grodansparadis/vscp-din-wireless-esp32-can-z102/design-documents/Z102_img/Z102_50.jpg

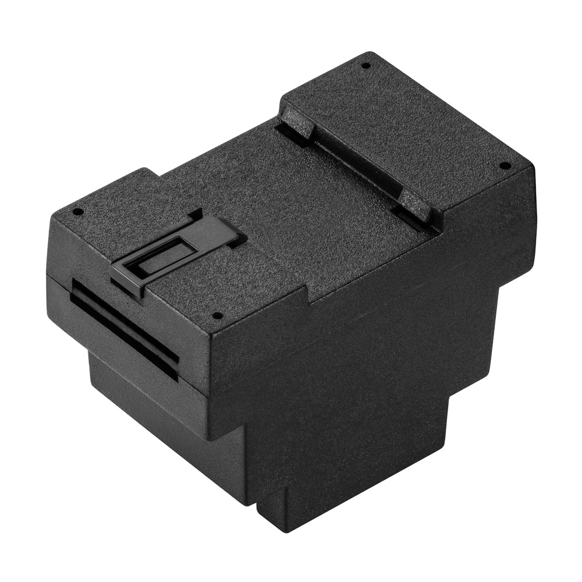
design-documents/Z102_img/Z102_50.jpg
