grodansparadis/vscp-din-wireless-esp32-can-z102/images/addr2line_error.png

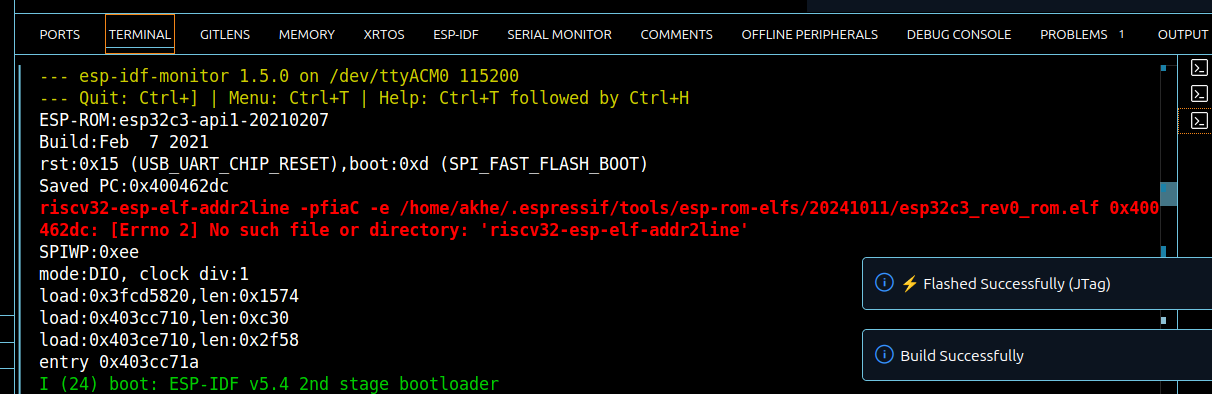
images/addr2line_error.png
