grodansparadis/vscp-din-wireless-esp32-can-z102/firmware/main/websrv.c

/*
  Web Server

  This file is part of the VSCP (https://www.vscp.org)

  The MIT License (MIT)
  Copyright (C) 2022-2026 Ake Hedman, the VSCP project <info@vscp.org>

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
  THE SOFTWARE IS PROVIDED "AS IS", WITHOUT WARRANTY OF ANY KIND, EXPRESS OR
  IMPLIED, INCLUDING BUT NOT LIMITED TO THE WARRANTIES OF MERCHANTABILITY,
  FITNESS FOR A PARTICULAR PURPOSE AND NONINFRINGEMENT. IN NO EVENT SHALL THE
  AUTHORS OR COPYRIGHT HOLDERS BE LIABLE FOR ANY CLAIM, DAMAGES OR OTHER
  LIABILITY, WHETHER IN AN ACTION OF CONTRACT, TORT OR OTHERWISE, ARISING FROM,
  OUT OF OR IN CONNECTION WITH THE SOFTWARE OR THE USE OR OTHER DEALINGS IN THE
  SOFTWARE.
*/

#include <stdio.h>
#include <string.h>
#include <ctype.h>
#include <stdarg.h>
#include <sys/param.h>
#include <sys/unistd.h>
#include <sys/stat.h>
#include <sys/socket.h>
#include <netinet/in.h>
#include <arpa/inet.h>
#include <dirent.h>

#include <esp_system.h>
#include <esp_chip_info.h>
#include <esp_flash_spi_init.h>
#include <esp_flash.h>
#include <esp_wifi.h>
#include <esp_mac.h>
#include <esp_ota_ops.h>
#include <esp_timer.h>
#include <esp_err.h>
#include <esp_log.h>
#include <nvs_flash.h>
#include <esp_http_server.h>

#include <esp_event_base.h>
#include <esp_tls_crypto.h>
#include <esp_vfs.h>
#include <esp_spiffs.h>
#include <network_provisioning/manager.h>
#include <cJSON.h>

#include <freertos/FreeRTOS.h>
#include <freertos/semphr.h>

#include <vscp.h>
#include <vscp-class.h>
#include <vscp-type.h>
#include <vscp-firmware-helper.h>

#include "urldecode.h"

#include "mqtt.h"
#include "main.h"
#include "vscp-ws1.h"
#include "websocksrv.h"
#include "websrv.h"
#include "udpsrv.h"
#include "build/build_counter.h"

#if !CONFIG_HTTPD_WS_SUPPORT
#error This code cannot be used unless HTTPD_WS_SUPPORT is enabled in esp-http-server component configuration
#endif

#ifdef CONFIG_EXAMPLE_PROV_TRANSPORT_BLE
#include <network_provisioning/scheme_ble.h>
#endif /* PROV_EXAMPLE_TRANSPORT_BLE */

#ifdef CONFIG_EXAMPLE_PROV_TRANSPORT_SOFTAP
#include <network_provisioning/scheme_softap.h>
#endif /* PROV_EXAMPLE_TRANSPORT_SOFTAP */

// #define MIN(a, b) (((a) < (b)) ? (a) : (b))
// #define MAX(a, b) (((a) > (b)) ? (a) : (b))

// From app_main
void
startOTA(void);
int
app_initiate_firmware_upload(const char *url);

// External from main
extern nvs_handle_t g_nvsHandle;
extern node_persistent_config_t g_persistent;
extern vprintf_like_t g_stdLogFunc;
extern transport_t tr_websockets;
extern transport_t tr_canapi;
extern transport_t tr_monitor;

// Extern from webnsocksrv
extern httpd_handle_t g_websocket_srv;

#define TAG __func__

static const char *
web_ui_version(const esp_app_desc_t *appDescr)
{
  static char s_ui_ver[64];
  const char *base = "0.0.0";

  if ((NULL != appDescr) && ('\0' != appDescr->version[0])) {
    base = appDescr->version;
  }

  snprintf(s_ui_ver, sizeof(s_ui_ver), "%s+b%d", base, BUILD_COUNTER);
  return s_ui_ver;
}

// Keep a short in-memory rolling log for the web UI.
#define WEB_LOG_RING_SIZE 200
#define WEB_LOG_LINE_MAX  192

typedef struct {
  uint32_t seq;
  char line[WEB_LOG_LINE_MAX];
} web_log_item_t;

static web_log_item_t g_web_log_ring[WEB_LOG_RING_SIZE];
static uint32_t g_web_log_seq = 0;
vprintf_like_t g_stdLogFunc   = NULL;
static SemaphoreHandle_t g_web_log_mutex = NULL;
static volatile bool s_web_log_route_in_progress = false;

static int web_log_vprintf(const char *fmt, va_list args);
static void web_log_capture_line(const char *line);
static esp_err_t logs_get_handler(httpd_req_t *req);
static esp_err_t logstream_get_handler(httpd_req_t *req);
static void web_log_hook_init(void);

// Max length a file path can have on storage
#define FILE_PATH_MAX (ESP_VFS_PATH_MAX + CONFIG_SPIFFS_OBJ_NAME_LEN)

// Chunk buffer size
#define CHUNK_BUFSIZE 8192

#define IS_FILE_EXT(filename, ext) (strcasecmp(&filename[strlen(filename) - sizeof(ext) + 1], ext) == 0)

// Prototypes

///////////////////////////////////////////////////////////////////////////////
// web_log_capture_line
//

static void
web_log_capture_line(const char *line)
{
  if ((NULL == line) || ('\0' == *line) || (NULL == g_web_log_mutex)) {
    return;
  }

  if (pdTRUE != xSemaphoreTake(g_web_log_mutex, pdMS_TO_TICKS(5))) {
    return;
  }

  uint32_t seq = ++g_web_log_seq;
  size_t idx   = (size_t) ((seq - 1U) % WEB_LOG_RING_SIZE);
  g_web_log_ring[idx].seq = seq;

  size_t j = 0;
  for (size_t i = 0; (line[i] != '\0') && (j < (WEB_LOG_LINE_MAX - 1)); ++i) {
    char c = line[i];
    if (('\r' == c) || ('\n' == c)) {
      if ((j > 0) && (' ' != g_web_log_ring[idx].line[j - 1])) {
        g_web_log_ring[idx].line[j++] = ' ';
      }
      continue;
    }
    g_web_log_ring[idx].line[j++] = c;
  }
  g_web_log_ring[idx].line[j] = '\0';

  xSemaphoreGive(g_web_log_mutex);
}

///////////////////////////////////////////////////////////////////////////////
// web_log_route_message
//
// Route log message to configured destination based on logType setting
//

static void
web_log_route_message(const char *message)
{
  if (NULL == message || '\0' == message[0]) {
    return;
  }

  // Route based on configured log type
  switch (g_persistent.logType) {
    
    case LOG_TYPE_UDP:
      // Send log message via configured logging destination.
      udpsrv_broadcast_message((const uint8_t *) message,
                               strlen(message),
                               g_persistent.logUrl,
                               g_persistent.logPort);
      break;

    case LOG_TYPE_MQTT:
      // Send log message via MQTT (if enabled)
      if (g_persistent.enableMqtt && strlen(g_persistent.logMqttTopic)) {
        mqtt_log((char *) message);
      }
      break;

    case LOG_TYPE_STD:
    case LOG_TYPE_TCP:
    case LOG_TYPE_HTTP:
    case LOG_TYPE_VSCP:
    case LOG_TYPE_NONE:
    default:
      // These are handled by the default logging mechanism or not used for syslog
      break;
  }
}

///////////////////////////////////////////////////////////////////////////////
// web_log_vprintf
//

static int
web_log_vprintf(const char *fmt, va_list args)
{
  if (NULL != fmt) {
    char line[WEB_LOG_LINE_MAX] = { 0 };
    va_list copy;
    va_copy(copy, args);
    int n = vsnprintf(line, sizeof(line), fmt, copy);
    va_end(copy);

    if (n > 0) {
      web_log_capture_line(line);

      // Prevent recursive routing when transport code itself logs.
      if (!s_web_log_route_in_progress) {
        s_web_log_route_in_progress = true;
        web_log_route_message(line);
        s_web_log_route_in_progress = false;
      }
    }
  }

  if (NULL != g_stdLogFunc) {
    return g_stdLogFunc(fmt, args);
  }

  return vprintf(fmt, args);
}

///////////////////////////////////////////////////////////////////////////////
// web_log_hook_init
//

static void
web_log_hook_init(void)
{
  if (NULL == g_web_log_mutex) {
    g_web_log_mutex = xSemaphoreCreateMutex();
  }

  if ((NULL != g_web_log_mutex) && (NULL == g_stdLogFunc)) {
    g_stdLogFunc = esp_log_set_vprintf(web_log_vprintf);
    ESP_LOGI(TAG, "Web log capture enabled");
  }
}

///////////////////////////////////////////////////////////////////////////////
// backup_add_hex_field
//

static void
backup_add_hex_field(cJSON *obj, const char *name, const uint8_t *data, size_t len)
{
  if ((NULL == obj) || (NULL == name) || (NULL == data) || (0 == len)) {
    return;
  }

  char *hex = (char *) calloc((len * 2) + 1, 1);
  if (NULL == hex) {
    return;
  }

  for (size_t i = 0; i < len; i++) {
    sprintf(hex + (i * 2), "%02X", data[i]);
  }

  cJSON_AddStringToObject(obj, name, hex);
  free(hex);
}

static uint32_t
backup_secret_seed(const char *field_name)
{
  uint32_t seed     = 2166136261u;
  const char *fixed = "VSCP-CFG-BACKUP-V1";

  for (size_t i = 0; fixed[i] != '\0'; i++) {
    seed ^= (uint8_t) fixed[i];
    seed *= 16777619u;
  }

  if (NULL != field_name) {
    for (size_t i = 0; field_name[i] != '\0'; i++) {
      seed ^= (uint8_t) field_name[i];
      seed *= 16777619u;
    }
  }

  if (0 == seed) {
    seed = 0x1A2B3C4Du;
  }

  return seed;
}

static uint32_t
backup_secret_next(uint32_t *state)
{
  *state ^= (*state << 13);
  *state ^= (*state >> 17);
  *state ^= (*state << 5);
  return *state;
}

static bool
backup_encrypt_to_hex(const char *field_name, const uint8_t *in, size_t in_len, char *out, size_t out_len)
{
  if ((NULL == in) || (NULL == out)) {
    return false;
  }

  if (out_len < ((in_len * 2) + 5)) {
    return false;
  }

  memcpy(out, "enc:", 4);
  uint32_t st = backup_secret_seed(field_name);

  for (size_t i = 0; i < in_len; i++) {
    uint8_t b = in[i] ^ (uint8_t) (backup_secret_next(&st) & 0xFF);
    sprintf(out + 4 + (i * 2), "%02X", b);
  }

  out[4 + (in_len * 2)] = '\0';
  return true;
}

static bool
backup_decrypt_from_hex(const char *field_name, const char *in, uint8_t *out, size_t out_len, size_t *written)
{
  if ((NULL == field_name) || (NULL == in) || (NULL == out)) {
    return false;
  }

  if (0 != strncmp(in, "enc:", 4)) {
    return false;
  }

  const char *hex = in + 4;
  size_t hex_len  = strlen(hex);
  if ((0 == hex_len) || (0 != (hex_len % 2))) {
    return false;
  }

  size_t need = hex_len / 2;
  if (need > out_len) {
    return false;
  }

  uint32_t st = backup_secret_seed(field_name);
  for (size_t i = 0; i < need; i++) {
    char h1 = hex[i * 2];
    char h2 = hex[(i * 2) + 1];
    if (!isxdigit((unsigned char) h1) || !isxdigit((unsigned char) h2)) {
      return false;
    }

    uint8_t hi = (uint8_t) ((h1 <= '9') ? (h1 - '0') : (10 + (tolower((unsigned char) h1) - 'a')));
    uint8_t lo = (uint8_t) ((h2 <= '9') ? (h2 - '0') : (10 + (tolower((unsigned char) h2) - 'a')));
    uint8_t b  = (uint8_t) ((hi << 4) | lo);
    out[i]     = b ^ (uint8_t) (backup_secret_next(&st) & 0xFF);
  }

  if (NULL != written) {
    *written = need;
  }

  return true;
}

static void
backup_add_encrypted_str_field(cJSON *obj, const char *name, const char *plain)
{
  if ((NULL == obj) || (NULL == name) || (NULL == plain)) {
    return;
  }

  size_t plain_len = strlen(plain);
  if (0 == plain_len) {
    cJSON_AddStringToObject(obj, name, "");
    return;
  }

  size_t out_len = (plain_len * 2) + 5;
  char *enc      = (char *) calloc(out_len, 1);
  if (NULL == enc) {
    cJSON_AddStringToObject(obj, name, "");
    return;
  }

  if (backup_encrypt_to_hex(name, (const uint8_t *) plain, plain_len, enc, out_len)) {
    cJSON_AddStringToObject(obj, name, enc);
  }
  else {
    cJSON_AddStringToObject(obj, name, "");
  }

  free(enc);
}

static void
backup_add_encrypted_blob_field(cJSON *obj, const char *name, const uint8_t *data, size_t data_len)
{
  if ((NULL == obj) || (NULL == name) || (NULL == data)) {
    return;
  }

  size_t out_len = (data_len * 2) + 5;
  char *enc      = (char *) calloc(out_len, 1);
  if (NULL == enc) {
    return;
  }

  if (backup_encrypt_to_hex(name, data, data_len, enc, out_len)) {
    cJSON_AddStringToObject(obj, name, enc);
  }

  free(enc);
}

//-----------------------------------------------------------------------------
//                               Start Basic Auth
//-----------------------------------------------------------------------------

///////////////////////////////////////////////////////////////////////////////
// http_auth_basic
//

static char *
http_auth_basic(const char *username, const char *password)
{
  int out;
  char *user_info = NULL;
  char *digest    = NULL;
  size_t n        = 0;
  asprintf(&user_info, "%s:%s", username, password);
  if (!user_info) {
    ESP_LOGE(TAG, "No enough memory for user information");
    return NULL;
  }
  esp_crypto_base64_encode(NULL, 0, &n, (const unsigned char *) user_info, strlen(user_info));

  /* 6: The length of the "Basic " string
   * n: Number of bytes for a base64 encode format
   * 1: Number of bytes for a reserved which be used to fill zero
   */
  digest = calloc(6 + n + 1, 1);
  if (digest) {
    strcpy(digest, "Basic ");
    esp_crypto_base64_encode((unsigned char *) digest + 6,
                             n,
                             (size_t *) &out,
                             (const unsigned char *) user_info,
                             strlen(user_info));
  }
  free(user_info);
  return digest;
}

///////////////////////////////////////////////////////////////////////////////
// info_get_handler
//
// HTTP GET handler for info page
//

static esp_err_t
info_get_handler(httpd_req_t *req)
{
  // esp_err_t rv;
  char *buf;
  char *temp;

  buf = (char *) calloc(CHUNK_BUFSIZE, 1);
  if (NULL == buf) {
    return ESP_ERR_NO_MEM;
  }

  temp = (char *) calloc(80, 1);
  if (NULL == temp) {
    return ESP_ERR_NO_MEM;
  }

  esp_chip_info_t chip_info;
  esp_chip_info(&chip_info);

  const esp_app_desc_t *appDescr = esp_app_get_description();

  sprintf(buf, WEBPAGE_START_TEMPLATE, g_persistent.nodeName, "Technical Node Info");
  httpd_resp_send_chunk(req, buf, HTTPD_RESP_USE_STRLEN);

  sprintf(buf, "<table style='width:100%%;margin-left: auto; margin-right: auto;'>");
  httpd_resp_send_chunk(req, buf, HTTPD_RESP_USE_STRLEN);

  // * * * system * * *);
  sprintf(buf, "<tr><td class='infoheader'>System</td><td></td></tr>");
  httpd_resp_send_chunk(req, buf, HTTPD_RESP_USE_STRLEN);

  sprintf(buf, "<tr style='padding: 25px;'><td class=\"name\">Chip type:</td>");
  httpd_resp_send_chunk(req, buf, HTTPD_RESP_USE_STRLEN);
  switch (chip_info.model) {

    case CHIP_ESP32:
      // printf("ESP32\n");
      sprintf(buf, "<td class=\"prop\">ESP32</td></tr>");
      break;

    case CHIP_ESP32S2:
      // printf("ESP32-S2\n");
      sprintf(buf, "<td class=\"prop\">ESP32-S2</td></tr>");
      break;

    case CHIP_ESP32S3:
      // printf("ESP32-S3\n");
      sprintf(buf, "<td class=\"prop\">ESP32-S3</td></tr>");
      break;

    case CHIP_ESP32C3:
      // printf("ESP32-C3\n");
      sprintf(buf, "<td class=\"prop\">ESP32-C3</td></tr>");
      break;

    case CHIP_ESP32H2:
      // printf("ESP32-H2\n");
      sprintf(buf, "<td class=\"prop\">ESP32-H2</td></tr>");
      break;

    case CHIP_ESP32C2:
      // printf("ESP32-C2\n");
      sprintf(buf, "<td class=\"prop\">ESP32-C2</td></tr>");
      break;

    default:
      // printf("Unknown\n");
      sprintf(buf, "<td class=\"prop\">Unknown</td></tr>");
      break;
  }
  httpd_resp_send_chunk(req, buf, HTTPD_RESP_USE_STRLEN);

  sprintf(buf, "<tr><td class=\"name\">Number of cores:</td><td class=\"prop\">%d</td></tr>", chip_info.cores);
  httpd_resp_send_chunk(req, buf, HTTPD_RESP_USE_STRLEN);

  // printf("Number of cores: %d \n", chip_info.cores);

  // Chip comm features
  sprintf(temp,
          "%s%s%s%s",
          (chip_info.features & CHIP_FEATURE_WIFI_BGN) ? "WiFi " : "",
          (chip_info.features & CHIP_FEATURE_BT) ? "BT " : "",
          (chip_info.features & CHIP_FEATURE_BLE) ? "BLE " : "",
          (chip_info.features & CHIP_FEATURE_IEEE802154) ? "802.15.4 " : "");
  sprintf(buf, "<tr><td class=\"name\">Chip comm features:</td><td class=\"prop\">%s</td></tr>", temp);
  httpd_resp_send_chunk(req, buf, HTTPD_RESP_USE_STRLEN);

  wifi_country_t country;
  esp_wifi_get_country(&country);
  // printf("Wifi country code: %c%c%c\n", country.cc[0],country.cc[1],country.cc[2]);
  sprintf(buf,
          "<tr><td class=\"name\">Wifi country code:</td><td class=\"prop\">%c%c%c</td></tr>",
          country.cc[0],
          country.cc[1],
          country.cc[2]);
  httpd_resp_send_chunk(req, buf, HTTPD_RESP_USE_STRLEN);

  sprintf(temp, "%s", (chip_info.features & CHIP_FEATURE_EMB_FLASH) ? "Yes" : "No");
  sprintf(buf, "<tr><td class=\"name\">Embedded flash:</td><td class=\"prop\">%s</td></tr>", temp);
  httpd_resp_send_chunk(req, buf, HTTPD_RESP_USE_STRLEN);

  sprintf(temp, "%s", (chip_info.features & CHIP_FEATURE_EMB_PSRAM) ? "Yes" : "No");
  sprintf(buf, "<tr><td class=\"name\">Embedded psram:</td><td class=\"prop\">%s</td></tr>", temp);
  httpd_resp_send_chunk(req, buf, HTTPD_RESP_USE_STRLEN);

  // sprintf(temp, "%d", chip_info.revision);
  sprintf(buf, "<tr><td class=\"name\">Silicon revision:</td><td class=\"prop\">%d</td></tr>", chip_info.revision);
  httpd_resp_send_chunk(req, buf, HTTPD_RESP_USE_STRLEN);

  uint32_t chipId;
  esp_flash_read_id(NULL, &chipId);
  // printf("Flash chip id: %04lX\n", chipId);
  sprintf(buf, "<tr><td class=\"name\">Flash chip id:</td><td class=\"prop\">%04lX</td></tr>", chipId);
  httpd_resp_send_chunk(req, buf, HTTPD_RESP_USE_STRLEN);

  uint64_t uniqueId;
  esp_flash_read_unique_chip_id(NULL, &uniqueId);
  // printf("Unique flash chip id: %08llX\n", uniqueId);
  sprintf(buf, "<tr><td class=\"name\">Unique flash chip id:</td><td class=\"prop\">%08llX</td></tr>", uniqueId);
  httpd_resp_send_chunk(req, buf, HTTPD_RESP_USE_STRLEN);

  uint32_t sizeFlash;
  esp_flash_get_size(NULL, &sizeFlash);
  sprintf(temp, "%s", (chip_info.features & CHIP_FEATURE_EMB_FLASH) ? "(embedded)" : "(external)");
  // printf("%luMB %s flash\n",
  //        sizeFlash / (1024 * 1024),
  //        (chip_info.features & CHIP_FEATURE_EMB_FLASH) ? "embedded" : "external");
  sprintf(buf,
          "<tr><td class=\"name\">Flash size:</td><td class=\"prop\">%s %lu MB</td></tr>",
          temp,
          sizeFlash / (1024 * 1024));
  httpd_resp_send_chunk(req, buf, HTTPD_RESP_USE_STRLEN);

  // get chip id
  // chipId = String((uint32_t) ESP.getEfuseMac(), HEX);
  // chipId.toUpperCase();
  // printf("Chip id: %s\n", chipId.c_str());

  // printf("esp-idf version: %s\n", esp_get_idf_version());
  sprintf(buf, "<tr><td class=\"name\">esp-idf version:</td><td class=\"prop\">%s</td></tr>", esp_get_idf_version());
  httpd_resp_send_chunk(req, buf, HTTPD_RESP_USE_STRLEN);

  // printf("Free heap size: %lu\n", esp_get_free_heap_size());
  sprintf(buf,
          "<tr><td class=\"name\">Free heap size:</td><td class=\"prop\">%lu kB (%lu)</td></tr>",
          esp_get_free_heap_size() / 1024,
          esp_get_free_heap_size());
  httpd_resp_send_chunk(req, buf, HTTPD_RESP_USE_STRLEN);

  // printf("Min free heap size: %lu\n", esp_get_minimum_free_heap_size());
  sprintf(buf,
          "<tr><td class=\"name\">Min free heap size:</td><td class=\"prop\">%lu kB (%lu)</td></tr>",
          esp_get_minimum_free_heap_size() / 1024,
          esp_get_minimum_free_heap_size());
  httpd_resp_send_chunk(req, buf, HTTPD_RESP_USE_STRLEN);

  // printf("Last reset reson: ");
  switch (esp_reset_reason()) {
    case ESP_RST_POWERON:
      sprintf(temp, "Reset due to power-on event.\n");
      break;
    case ESP_RST_EXT:
      sprintf(temp, "Reset by external pin (not applicable for ESP32.\n");
      break;
    case ESP_RST_SW:
      sprintf(temp, "Software reset via esp_restart.\n");
      break;
    case ESP_RST_PANIC:
      sprintf(temp, "Software reset due to exception/panic.\n");
      break;
    case ESP_RST_INT_WDT:
      sprintf(temp, "Reset (software or hardware) due to interrupt watchdog.\n");
      break;
    case ESP_RST_TASK_WDT:
      sprintf(temp, "Reset due to task watchdog.\n");
      break;
    case ESP_RST_WDT:
      sprintf(temp, "Reset due to other watchdogs.\n");
      break;
    case ESP_RST_DEEPSLEEP:
      sprintf(temp, "Reset after exiting deep sleep mode.\n");
      break;
    case ESP_RST_BROWNOUT:
      sprintf(temp, "Brownout reset (software or hardware.\n");
      break;
    case ESP_RST_SDIO:
      sprintf(temp, "Reset over SDIO.\n");
      break;
    case ESP_RST_UNKNOWN:
    default:
      sprintf(temp, "Reset reason can not be determined.\n");
      break;
  }
  sprintf(buf, "<tr><td class=\"name\">Last reset reason:</td><td class=\"prop\">%s</td></tr>", temp);
  httpd_resp_send_chunk(req, buf, HTTPD_RESP_USE_STRLEN);

  sprintf(buf, "<tr><td class=\"name\">Number of reboots:</td><td class=\"prop\">%lu</td></tr>", g_persistent.bootCnt);
  httpd_resp_send_chunk(req, buf, HTTPD_RESP_USE_STRLEN);

  char *bufguid = (char *) calloc(50, 1);
  if (NULL != bufguid) {
    vscp_fwhlp_writeGuidToString(bufguid, g_persistent.guid);
    sprintf(buf, "<tr><td class=\"name\">GUID:</td><td class=\"prop\">%s</td></tr>", bufguid);
    httpd_resp_send_chunk(req, buf, HTTPD_RESP_USE_STRLEN);
    free(bufguid);
  }

  // -------------------------------------------------------------------------

  // * * *  Application * * *
  // sprintf(buf, "<tr><td>Application</td><td></td></tr>");
  sprintf(buf, "<tr><td class='infoheader'>Application</td><td></td></tr>");
  httpd_resp_send_chunk(req, buf, HTTPD_RESP_USE_STRLEN);

  int64_t time = esp_timer_get_time();
  int64_t seconds = time / 1000000;
  sprintf(buf,
          "<tr><td class=\"name\">Uptime:</td><td class=\"prop\">%lldT%02lld:%02lld:%02lld</td></tr>",
          seconds / (3600 * 24),
          (seconds % (3600 * 24)) / 3600,
          (seconds % 3600) / 60,
          seconds % 60);
  httpd_resp_send_chunk(req, buf, HTTPD_RESP_USE_STRLEN);

  if (NULL != appDescr) {
    // sprintf(temp,"%s",appDescr->project_name);
    sprintf(buf, "<tr><td class=\"name\">Application:</td><td class=\"prop\">%s</td></tr>", appDescr->project_name);
    httpd_resp_send_chunk(req, buf, HTTPD_RESP_USE_STRLEN);

    // sprintf(temp,"Application ver: %s\n",appDescr->version);
        sprintf(buf,
          "<tr><td class=\"name\">Application ver:</td><td class=\"prop\">%s</td></tr>",
          web_ui_version(appDescr));
    httpd_resp_send_chunk(req, buf, HTTPD_RESP_USE_STRLEN);

    // sprintf(temp,"Application ver: %s %s\n",appDescr->date,appDescr->time);
    sprintf(buf,
            "<tr><td class=\"name\">Compile time:</td><td class=\"prop\">%s %s</td></tr>",
            appDescr->date,
            appDescr->time);
    httpd_resp_send_chunk(req, buf, HTTPD_RESP_USE_STRLEN);

    // sprintf(temp,"idf ver: %s\n",appDescr->idf_ver);
    sprintf(buf, "<tr><td class=\"name\">Compiled w/ idf ver:</td><td class=\"prop\">%s</td></tr>", appDescr->idf_ver);
    httpd_resp_send_chunk(req, buf, HTTPD_RESP_USE_STRLEN);
  }

  // * * *  CAN/TWAI * * *
  sprintf(buf, "<tr><td class='infoheader'>CAN/TWAI Interface</td><td></td></tr>");
  httpd_resp_send_chunk(req, buf, HTTPD_RESP_USE_STRLEN);

  // CAN Mode
  const char *canModeStr = (g_persistent.canMode == 0) ? "Normal" : "Listen Only";
  sprintf(buf, "<tr><td class=\"name\">CAN Mode:</td><td class=\"prop\">%s</td></tr>", canModeStr);
  httpd_resp_send_chunk(req, buf, HTTPD_RESP_USE_STRLEN);

  // CAN Speed
  const char *canSpeedStr;
  switch (g_persistent.canSpeed) {
    case 0:
      canSpeedStr = "5 Kbps";
      break;
    case 1:
      canSpeedStr = "10 Kbps";
      break;
    case 2:
      canSpeedStr = "20 Kbps";
      break;
    case 3:
      canSpeedStr = "25 Kbps";
      break;
    case 4:
      canSpeedStr = "50 Kbps";
      break;
    case 5:
      canSpeedStr = "100 Kbps";
      break;
    case 6:
      canSpeedStr = "125 Kbps";
      break;
    case 7:
      canSpeedStr = "250 Kbps";
      break;
    case 8:
      canSpeedStr = "500 Kbps";
      break;
    case 9:
      canSpeedStr = "800 Kbps";
      break;
    case 10:
      canSpeedStr = "1000 Kbps";
      break;
    default:
      canSpeedStr = "Unknown";
      break;
  }
  sprintf(buf, "<tr><td class=\"name\">CAN Speed:</td><td class=\"prop\">%s</td></tr>", canSpeedStr);
  httpd_resp_send_chunk(req, buf, HTTPD_RESP_USE_STRLEN);

  // CAN Filter
  sprintf(buf,
          "<tr><td class=\"name\">CAN Filter:</td><td class=\"prop\">0x%08X</td></tr>",
          (unsigned int) g_persistent.canFilter);
  httpd_resp_send_chunk(req, buf, HTTPD_RESP_USE_STRLEN);

  // Messages Sent
  sprintf(buf,
          "<tr><td class=\"name\">Messages Sent:</td><td class=\"prop\">%u</td></tr>",
          (unsigned int) g_persistent.nSent);
  httpd_resp_send_chunk(req, buf, HTTPD_RESP_USE_STRLEN);

  // Messages Received
  sprintf(buf,
          "<tr><td class=\"name\">Messages Received:</td><td class=\"prop\">%u</td></tr>",
          (unsigned int) g_persistent.nRecv);
  httpd_resp_send_chunk(req, buf, HTTPD_RESP_USE_STRLEN);

  // Total Errors
  sprintf(buf,
          "<tr><td class=\"name\">Total Errors:</td><td class=\"prop\">%u</td></tr>",
          (unsigned int) g_persistent.nErr);
  httpd_resp_send_chunk(req, buf, HTTPD_RESP_USE_STRLEN);

  // Last Error Code
  sprintf(buf,
          "<tr><td class=\"name\">Last Error Code:</td><td class=\"prop\">0x%08X</td></tr>",
          (unsigned int) g_persistent.lastError);
  httpd_resp_send_chunk(req, buf, HTTPD_RESP_USE_STRLEN);

  // * * *  Connection * * *
  sprintf(buf, "<tr><td class='infoheader'>Connection</td><td></td></tr>");
  httpd_resp_send_chunk(req, buf, HTTPD_RESP_USE_STRLEN);

  wifi_mode_t mode;
  esp_wifi_get_mode(&mode);
  switch (mode) {

    case WIFI_MODE_STA:
      sprintf(temp, "STA\n");
      break;

    case WIFI_MODE_AP:
      sprintf(temp, "AP\n");
      break;

    case WIFI_MODE_APSTA:
      sprintf(temp, "APSTA\n");
      break;

    case WIFI_MODE_NULL:
    default:
      sprintf(temp, "unknown\n");
      break;
  };
  // sprintf(temp,"Wifi mode: ");
  sprintf(buf, "<tr><td class=\"name\">Wifi mode:</td><td class=\"prop\">%s</td></tr>", temp);
  httpd_resp_send_chunk(req, buf, HTTPD_RESP_USE_STRLEN);

  wifi_sta_list_t sta;
  esp_wifi_ap_get_sta_list(&sta);
  // printf("Stations: %d\n",sta.num);
  sprintf(buf, "<tr><td class=\"name\">Stations:</td><td class=\"prop\">%d</td></tr>", sta.num);
  httpd_resp_send_chunk(req, buf, HTTPD_RESP_USE_STRLEN);

  wifi_ap_record_t ap_info;
  esp_wifi_sta_get_ap_info(&ap_info);
  // printf("bssid: " MACSTR "\n", MAC2STR(ap_info.bssid));
  sprintf(buf, "<tr><td class=\"name\">bssid:</td><td class=\"prop\">" MACSTR "</td></tr>", MAC2STR(ap_info.bssid));
  httpd_resp_send_chunk(req, buf, HTTPD_RESP_USE_STRLEN);

  // printf("ssid: %s\n", ap_info.ssid);
  sprintf(buf, "<tr><td class=\"name\">ssid:</td><td class=\"prop\">%s</td></tr>", ap_info.ssid);
  httpd_resp_send_chunk(req, buf, HTTPD_RESP_USE_STRLEN);

  // printf("channel: %d (%d)\n", ap_info.primary, ap_info.second);
  sprintf(buf,
          "<tr><td class=\"name\">channel:</td><td class=\"prop\">%d (%d)</td></tr>",
          ap_info.primary,
          ap_info.second);
  httpd_resp_send_chunk(req, buf, HTTPD_RESP_USE_STRLEN);

  // printf("signal strength: %d\n", ap_info.rssi);
  if (ap_info.rssi > -30) {
    sprintf(temp, "Perfect");
  }
  else if (ap_info.rssi > -50) {
    sprintf(temp, "Excellent");
  }
  else if (ap_info.rssi > -60) {
    sprintf(temp, "Good");
  }
  else if (ap_info.rssi > -67) {
    sprintf(temp, "Limited");
  }
  else if (ap_info.rssi > -70) {
    sprintf(temp, "Poor");
  }
  else if (ap_info.rssi > -80) {
    sprintf(temp, "Unstable");
  }
  else {
    sprintf(temp, "Unusable");
  }

  sprintf(buf,
          "<tr><td class=\"name\">signal strength:</td><td class=\"prop\">%d dBm ( %d%% = %s)</td></tr>",
          ap_info.rssi,
          (2 * (ap_info.rssi + 100)),
          temp);
  httpd_resp_send_chunk(req, buf, HTTPD_RESP_USE_STRLEN);

  // printf("Mode: 11%s%s%s %s %s",
  //           ap_info.phy_11b ? "b" : "",
  //           ap_info.phy_11g ? "g" : "",
  //           ap_info.phy_11n ? "n" : "",
  //           ap_info.phy_lr ? "lr" : "",
  //           ap_info.wps ? "wps" : "");
  // printf("\nAuth mode of AP: ");
  switch (ap_info.authmode) {

    case WIFI_AUTH_OPEN:
      sprintf(temp, "open\n");
      break;

    case WIFI_AUTH_WEP:
      sprintf(temp, "wep\n");
      break;

    case WIFI_AUTH_WPA_PSK:
      sprintf(temp, "wpa-psk\n");
      break;

    case WIFI_AUTH_WPA2_PSK:
      sprintf(temp, "wpa2-psk\n");
      break;

    case WIFI_AUTH_WPA_WPA2_PSK:
      sprintf(temp, "wpa-wpa2-psk\n");
      break;

    case WIFI_AUTH_WPA2_ENTERPRISE:
      sprintf(temp, "wpa2-enterprise\n");
      break;

    case WIFI_AUTH_WPA3_PSK:
      sprintf(temp, "wpa3-psk\n");
      break;

    case WIFI_AUTH_WPA2_WPA3_PSK:
      sprintf(temp, "wpa2-wpa3-psk\n");
      break;

    case WIFI_AUTH_WAPI_PSK:
      sprintf(temp, "wpa2-wapi-psk\n");
      break;

    case WIFI_AUTH_OWE:
      sprintf(temp, "wpa2-wapi-psk\n");
      break;

    default:
      sprintf(temp, "unknown\n");
      break;
  }

  sprintf(buf, "<tr><td class=\"name\">Auth mode of AP:</td><td class=\"prop\">%s</td></tr>", temp);
  httpd_resp_send_chunk(req, buf, HTTPD_RESP_USE_STRLEN);

  uint8_t mac[6];
  esp_wifi_get_mac(ESP_MAC_WIFI_STA, mac);
  // printf("Wifi STA MAC address: " MACSTR "\n", MAC2STR(mac));
  sprintf(buf,
          "<tr><td class=\"name\">Wifi STA MAC address:</td><td class=\"prop\">" MACSTR "</td></tr>",
          MAC2STR(mac));
  httpd_resp_send_chunk(req, buf, HTTPD_RESP_USE_STRLEN);

  esp_wifi_get_mac(ESP_MAC_WIFI_SOFTAP, mac);
  // printf("Wifi SOFTAP MAC address: " MACSTR "\n", MAC2STR(mac));
  sprintf(buf,
          "<tr><td class=\"name\">Wifi SOFTAP MAC address:</td><td class=\"prop\">" MACSTR "</td></tr>",
          MAC2STR(mac));
  httpd_resp_send_chunk(req, buf, HTTPD_RESP_USE_STRLEN);

  esp_netif_t *netif = NULL;
  netif              = esp_netif_get_handle_from_ifkey("WIFI_STA_DEF");
  esp_netif_ip_info_t ifinfo;
  if (NULL != netif) {
    esp_netif_get_ip_info(netif, &ifinfo);
    // printf("IP address (wifi): " IPSTR "\n", IP2STR(&ifinfo.ip));
    sprintf(buf,
            "<tr><td class=\"name\">IP address (wifi):</td><td class=\"prop\">" IPSTR "</td></tr>",
            IP2STR(&ifinfo.ip));
    httpd_resp_send_chunk(req, buf, HTTPD_RESP_USE_STRLEN);

    // printf("Subnet Mask: " IPSTR "\n", IP2STR(&ifinfo.netmask));
    sprintf(buf,
            "<tr><td class=\"name\">Subnet Mask:</td><td class=\"prop\">" IPSTR "</td></tr>",
            IP2STR(&ifinfo.netmask));
    httpd_resp_send_chunk(req, buf, HTTPD_RESP_USE_STRLEN);

    // printf("Gateway: " IPSTR "\n", IP2STR(&ifinfo.gw));
    sprintf(buf, "<tr><td class=\"name\">Gateway:</td><td class=\"prop\">" IPSTR "</td></tr>", IP2STR(&ifinfo.gw));
    httpd_resp_send_chunk(req, buf, HTTPD_RESP_USE_STRLEN);

    esp_netif_dns_info_t dns;
    esp_netif_get_dns_info(netif, ESP_NETIF_DNS_MAIN, &dns);
    // printf("DNS DNS Server1: " IPSTR "\n", IP2STR(&dns.ip.u_addr.ip4));
    sprintf(buf,
            "<tr><td class=\"name\">DNS Server1:</td><td class=\"prop\">" IPSTR "</td></tr>",
            IP2STR(&dns.ip.u_addr.ip4));
    httpd_resp_send_chunk(req, buf, HTTPD_RESP_USE_STRLEN);
    esp_netif_get_dns_info(netif, ESP_NETIF_DNS_BACKUP, &dns);

    // printf("DNS Server2: " IPSTR "\n", IP2STR(&dns.ip.u_addr.ip4));
    sprintf(buf,
            "<tr><td class=\"name\">DNS Server2:</td><td class=\"prop\">" IPSTR "</td></tr>",
            IP2STR(&dns.ip.u_addr.ip4));
    httpd_resp_send_chunk(req, buf, HTTPD_RESP_USE_STRLEN);
  }

  sprintf(buf, "</table>");
  httpd_resp_send_chunk(req, buf, HTTPD_RESP_USE_STRLEN);

  sprintf(buf, WEBPAGE_END_TEMPLATE, web_ui_version(appDescr), g_persistent.nodeName);
  httpd_resp_send_chunk(req, buf, HTTPD_RESP_USE_STRLEN);

  httpd_resp_send_chunk(req, NULL, 0);

  free(buf);
  free(temp);

  return ESP_OK;
}

// URI handler for getting uploaded files
httpd_uri_t info = { .uri = "/info", .method = HTTP_GET, .handler = info_get_handler, .user_ctx = NULL };

///////////////////////////////////////////////////////////////////////////////
// reset_get_handler
//
// HTTP GET handler for reset of machine
//

static esp_err_t
reset_get_handler(httpd_req_t *req)
{
  const char *resp_str = "<html><head><meta charset='utf-8'><meta http-equiv=\"refresh\" content=\"2;url=index.html\" "
                         "/></head><body><h1>The system is restarting...</h1></body></html>";
  httpd_resp_send(req, resp_str, HTTPD_RESP_USE_STRLEN);

  // Let content render
  vTaskDelay(2000 / portTICK_PERIOD_MS);

  // esp_wifi_disconnect();
  // vTaskDelay(2000 / portTICK_PERIOD_MS);
  esp_restart();
  return ESP_OK;
}

httpd_uri_t reset = { .uri = "/reset", .method = HTTP_GET, .handler = reset_get_handler, .user_ctx = NULL };

///////////////////////////////////////////////////////////////////////////////
// upgrade_get_handler
//
// HTTP GET handler for update of firmware
//

static esp_err_t
send_restart_info_page(httpd_req_t *req, const char *message)
{
  httpd_resp_sendstr_chunk(req, "<html><head><meta charset='utf-8'><meta http-equiv=\"refresh\" content=\"2;url=index.html\" /><style>");
  httpd_resp_sendstr_chunk(req, WEBPAGE_STYLE_CSS);
  httpd_resp_sendstr_chunk(req,
                           "</style></head><body><div style='text-align:left;display:inline-block;color:#eaeaea;min-width:340px;max-width:600px;'>"
                           "<div style='text-align:center;color:#eaeaea;'><h3>");
  httpd_resp_sendstr_chunk(req, g_persistent.nodeName);
  httpd_resp_sendstr_chunk(req,
                           "</h3></div><div style='text-align:center;color:#f7f1a6;'><h4>");
  httpd_resp_sendstr_chunk(req, message);
  httpd_resp_sendstr_chunk(
    req,
    "</h4></div><p class=\"prop\" style='text-align:center;'>The page will reconnect automatically after the restart.</p></div></body></html>");

  return httpd_resp_sendstr_chunk(req, NULL);
}
// - Server upgrade
// - Local upgrade
//

static esp_err_t
upgrade_get_handler(httpd_req_t *req)
{
  // esp_err_t rv;
  char *buf;
  char *temp;

  buf = (char *) calloc(CHUNK_BUFSIZE, 1);
  if (NULL == buf) {
    return ESP_ERR_NO_MEM;
  }

  temp = (char *) calloc(80, 1);
  if (NULL == temp) {
    return ESP_ERR_NO_MEM;
  }

  esp_chip_info_t chip_info;
  esp_chip_info(&chip_info);

  const esp_app_desc_t *appDescr = esp_app_get_description();

  sprintf(buf, WEBPAGE_START_TEMPLATE, g_persistent.nodeName, "Upgrade firmware");
  httpd_resp_send_chunk(req, buf, HTTPD_RESP_USE_STRLEN);

  sprintf(buf, "<h3>Upgrade from web server</h3>");
  httpd_resp_send_chunk(req, buf, HTTPD_RESP_USE_STRLEN);

  sprintf(buf, "<div><form id=but3 class=\"button\" action='/upgrdsrv' method='get'><fieldset>");
  httpd_resp_send_chunk(req, buf, HTTPD_RESP_USE_STRLEN);

  sprintf(buf, "OTA URL:<input type=\"text\"  id=\"url\" name=\"url\" value=\"%s\" >", DEFAULT_APP_OTA_URL);
  httpd_resp_send_chunk(req, buf, HTTPD_RESP_USE_STRLEN);

  sprintf(buf, "<button class=\"bgrn bgrn:hover\" >Start Upgrade</button></fieldset></form></div>");
  httpd_resp_send_chunk(req, buf, HTTPD_RESP_USE_STRLEN);

  // ----- Local -----

  sprintf(buf,
          "<h3>Upgrade from local file</h3><div> <span style=\"color:red;font-family:verdana;font-size:300%%;\" "
          "id=\"progress\" /></div>");
  httpd_resp_send_chunk(req, buf, HTTPD_RESP_USE_STRLEN);

  sprintf(buf, "<div><fform id=but3 class=\"button\" action='/upgrdlocal' method='post'><fieldset>");
  httpd_resp_send_chunk(req, buf, HTTPD_RESP_USE_STRLEN);

  sprintf(buf,
          "<label for=\"otafile\">OTA firmware file:</label><input type=\"file\" id=\"otafile\" name=\"otafile\" />");
  httpd_resp_send_chunk(req, buf, HTTPD_RESP_USE_STRLEN);

  sprintf(buf,
          "<button class=\"bgrn bgrn:hover\" id=\"upload\" onclick=\"startUpload();\">Start "
          "Upgrade</button></fieldset></fform></div>");
  httpd_resp_send_chunk(req, buf, HTTPD_RESP_USE_STRLEN);

  sprintf(buf, WEBPAGE_END_TEMPLATE, web_ui_version(appDescr), g_persistent.nodeName);
  httpd_resp_send_chunk(req, buf, HTTPD_RESP_USE_STRLEN);

  httpd_resp_send_chunk(req, NULL, 0);

  free(buf);
  free(temp);

  return ESP_OK;
}

// httpd_uri_t upgrade = { .uri = "/upgrade", .method = HTTP_GET, .handler = upgrade_get_handler, .user_ctx = NULL };

///////////////////////////////////////////////////////////////////////////////
// upgrdsrv_get_handler
//

static esp_err_t
upgrdsrv_get_handler(httpd_req_t *req)
{
  esp_err_t ret;
  char *buf = NULL;
  char *req_buf;
  size_t req_buf_len;

  buf = (char *) calloc(CHUNK_BUFSIZE, 1);
  if (NULL == buf) {
    return ESP_ERR_NO_MEM;
  }

  // Read URL query string length and allocate memory for length + 1,
  // extra byte for null termination
  req_buf_len = httpd_req_get_url_query_len(req) + 1;
  if (req_buf_len > 1) {
    req_buf = (char *) malloc(req_buf_len);
    if (httpd_req_get_url_query_str(req, req_buf, req_buf_len) == ESP_OK) {

      ESP_LOGD(TAG, "Found URL query => %s", req_buf);
      char *param = (char *) malloc(WEBPAGE_PARAM_SIZE);
      if (NULL == param) {
        free(req_buf);
        free(buf);
        return ESP_ERR_NO_MEM;
      }

      // URL
      if (ESP_OK == (ret = httpd_query_key_value(req_buf, "url", param, WEBPAGE_PARAM_SIZE))) {
        ESP_LOGD(TAG, "Found query parameter => url=%s", param);
      }
      else {
        ESP_LOGE(TAG, "Error getting url => rv=%d", ret);
      }

      free(param);
    }

    free(req_buf);
  }

  free(buf);

  const char *resp_str = "<html><head><meta charset='utf-8'><meta http-equiv=\"refresh\" content=\"10;url=index.html\" "
                         "/></head><body><h1>Firmware upgrade in progress...</h1></body></html>";
  httpd_resp_send(req, resp_str, HTTPD_RESP_USE_STRLEN);

  // Let content render
  vTaskDelay(2000 / portTICK_PERIOD_MS);

  printf("Start OTA\n");

  // Start the OTA task
  startOTA();

  return ESP_OK;
}

///////////////////////////////////////////////////////////////////////////////
// upgrdlocal_post_handler
//
// Handle OTA file upload
// https://github.com/Jeija/esp32-softap-ota
//

esp_err_t
upgrdlocal_post_handler(httpd_req_t *req)
{
  char buf[1000];
  esp_ota_handle_t ota_handle;
  int remaining = req->content_len;

  const esp_partition_t *ota_partition = esp_ota_get_next_update_partition(NULL);
  ESP_ERROR_CHECK(esp_ota_begin(ota_partition, OTA_SIZE_UNKNOWN, &ota_handle));

  while (remaining > 0) {

    ESP_LOGD(TAG, "OTA remaining %d", remaining);

    int recv_len = httpd_req_recv(req, buf, MIN(remaining, sizeof(buf)));

    // Timeout Error: Just retry
    if (recv_len == HTTPD_SOCK_ERR_TIMEOUT) {
      continue;
    }
    else if (recv_len <= 0) {
      // Serious Error: Abort OTA
      ESP_LOGE(TAG, "OTA aborted due to protocol error");
      httpd_resp_send_err(req, HTTPD_500_INTERNAL_SERVER_ERROR, "Protocol Error");
      return ESP_FAIL;
    }

    // Successful Upload: Flash firmware chunk
    if (esp_ota_write(ota_handle, (const void *) buf, recv_len) != ESP_OK) {
      ESP_LOGE(TAG, "OTA aborted due to flash error");
      httpd_resp_send_err(req, HTTPD_500_INTERNAL_SERVER_ERROR, "Flash Error");
      return ESP_FAIL;
    }

    remaining -= recv_len;
  }

  // Validate and switch to new OTA image and reboot
  if (esp_ota_end(ota_handle) != ESP_OK || esp_ota_set_boot_partition(ota_partition) != ESP_OK) {
    ESP_LOGE(TAG, "OTA failed due to image activation error");
    httpd_resp_send_err(req, HTTPD_500_INTERNAL_SERVER_ERROR, "Validation / Activation Error");
    return ESP_FAIL;
  }

  ESP_LOGD(TAG, "OTA finished");

  // httpd_resp_sendstr(req, "Firmware update complete, rebooting now!\n");
  const char *resp_str = "<html><head><meta charset='utf-8'><meta http-equiv=\"refresh\" content=\"2;url=index.html\" "
                         "/></head><body><h1>Firmware update complete, rebooting now!...</h1></body></html>";
  httpd_resp_send(req, resp_str, HTTPD_RESP_USE_STRLEN);

  // Let content render
  vTaskDelay(500 / portTICK_PERIOD_MS);
  esp_restart();

  return ESP_OK;
}

static const httpd_uri_t upgrdlocal = { .uri      = "/upgrdlocal",
                                        .method   = HTTP_POST,
                                        .handler  = upgrdlocal_post_handler,
                                        .user_ctx = NULL };

///////////////////////////////////////////////////////////////////////////////
// upgrdsibling_get_handler
//
static esp_err_t
upgrdsibling_get_handler(httpd_req_t *req)
{
  esp_err_t ret;
  char *buf = NULL;
  char *req_buf;
  size_t req_buf_len;
  char url[DEFAULT_APP_OTA_URL_MAX_SIZE];

  buf = (char *) calloc(CHUNK_BUFSIZE, 1);
  if (NULL == buf) {
    return ESP_ERR_NO_MEM;
  }

  // Read URL query string length and allocate memory for length + 1,
  // extra byte for null termination
  req_buf_len = httpd_req_get_url_query_len(req) + 1;
  if (req_buf_len > 1) {
    req_buf = (char *) malloc(req_buf_len);
    if (httpd_req_get_url_query_str(req, req_buf, req_buf_len) == ESP_OK) {

      ESP_LOGD(TAG, "Found URL query => %s", req_buf);
      char *param = (char *) malloc(WEBPAGE_PARAM_SIZE);
      if (NULL == param) {
        free(req_buf);
        free(buf);
        return ESP_ERR_NO_MEM;
      }

      // URL
      if (ESP_OK == (ret = httpd_query_key_value(req_buf, "url", param, WEBPAGE_PARAM_SIZE))) {

        char *pdecoded = urlDecode(param);
        if (NULL == pdecoded) {
          free(param);
          free(req_buf);
          free(buf);
          return ESP_ERR_NO_MEM;
        }

        memset(url, 0, DEFAULT_APP_OTA_URL_MAX_SIZE);
        strncpy(url, pdecoded, MIN(strlen(pdecoded), (DEFAULT_APP_OTA_URL_MAX_SIZE - 1)));

        ESP_LOGD(TAG, "Found query parameter => url=%s", url);

        free(pdecoded);
      }
      else {
        ESP_LOGE(TAG, "Error getting url => rv=%d", ret);
      }

      free(param);
    }

    free(req_buf);
  }

  free(buf);

  const char *resp_str = "<html><head><meta charset='utf-8'><meta http-equiv=\"refresh\" content=\"10;url=index.html\" "
                         "/></head><body><h1>Firmware upgrade of sibling in progress...</h1></body></html>";
  httpd_resp_send(req, resp_str, HTTPD_RESP_USE_STRLEN);

  // Let content render
  vTaskDelay(2000 / portTICK_PERIOD_MS);

  printf("Start OTA update of beta/gamma node(s)  url=%s\n", url);

  // Start the OTA task

  ret = app_initiate_firmware_upload(url);
  if (ESP_OK != ret) {
    ESP_LOGE(TAG, "Initiation of sibling firmware upload failed ret=%x", ret);
    return ret;
  }

  return ESP_OK;
}

///////////////////////////////////////////////////////////////////////////////
// upgrdlocal_post_handler
//
// Handle OTA file upload
// https://github.com/Jeija/esp32-softap-ota
//

esp_err_t
upgrdSiblingslocal_post_handler(httpd_req_t *req)
{
  char buf[1000];
  uint8_t sha_256[32] = { 0 };
  esp_ota_handle_t ota_handle;
  int remaining = req->content_len;

  const esp_partition_t *ota_partition = esp_ota_get_next_update_partition(NULL);
  ESP_ERROR_CHECK(esp_ota_begin(ota_partition, OTA_SIZE_UNKNOWN, &ota_handle));

  while (remaining > 0) {

    ESP_LOGD(TAG, "OTA remaining %d", remaining);

    taskYIELD();

    int recv_len = httpd_req_recv(req, buf, MIN(remaining, sizeof(buf)));

    // Timeout Error: Just retry
    if (recv_len == HTTPD_SOCK_ERR_TIMEOUT) {
      continue;
    }
    else if (recv_len <= 0) {
      // Serious Error: Abort OTA
      ESP_LOGE(TAG, "OTA aborted due to protocol error");
      httpd_resp_send_err(req, HTTPD_500_INTERNAL_SERVER_ERROR, "Protocol Error");
      return ESP_FAIL;
    }

    // Successful Upload: Flash firmware chunk
    if (esp_ota_write(ota_handle, (const void *) buf, recv_len) != ESP_OK) {
      ESP_LOGE(TAG, "OTA aborted due to flash error");
      httpd_resp_send_err(req, HTTPD_500_INTERNAL_SERVER_ERROR, "Flash Error");
      return ESP_FAIL;
    }

    remaining -= recv_len;
  }

  // Validate and switch to new OTA image and reboot
  if (esp_ota_end(ota_handle) != ESP_OK /*|| esp_ota_set_boot_partition(ota_partition) != ESP_OK*/) {
    ESP_LOGE(TAG, "OTA failed due to image activation error");
    httpd_resp_send_err(req, HTTPD_500_INTERNAL_SERVER_ERROR, "Validation / Activation Error");
    return ESP_FAIL;
  }

  ESP_LOGD(TAG, "Send OTA to sibling(s)");

  esp_partition_get_sha256(ota_partition, sha_256);

  // Send new firmware to clients
  // app_firmware_send(req->content_len, sha_256);

  ESP_LOGD(TAG, "Images sent to sibling(s)");

  // httpd_resp_sendstr(req, "Firmware update complete, rebooting now!\n");
  const char *resp_str = "<html><head><meta charset='utf-8'><meta http-equiv=\"refresh\" content=\"2;url=index.html\" "
                         "/></head><body><h1>Firmware update complete, rebooting now!...</h1></body></html>";
  httpd_resp_send(req, resp_str, HTTPD_RESP_USE_STRLEN);

  return ESP_OK;
}

static const httpd_uri_t upgrdsiblinglocal = { .uri      = "/upgrdSiblingLocal",
                                               .method   = HTTP_POST,
                                               .handler  = upgrdSiblingslocal_post_handler,
                                               .user_ctx = NULL };

///////////////////////////////////////////////////////////////////////////////
// hello_get_handler
//
// Copies the full path into destination buffer and returns
// pointer to path (skipping the preceding base path)
//

static const char *
get_path_from_uri(char *dest, const char *base_path, const char *uri, size_t destsize)
{
  const size_t base_pathlen = strlen(base_path);
  size_t pathlen            = strlen(uri);

  const char *quest = strchr(uri, '?');
  if (quest) {
    pathlen = MIN(pathlen, quest - uri);
  }
  const char *hash = strchr(uri, '#');
  if (hash) {
    pathlen = MIN(pathlen, hash - uri);
  }

  if (base_pathlen + pathlen + 1 > destsize) {
    // Full path string won't fit into destination buffer
    return NULL;
  }

  // Construct full path (base + path)
  strcpy(dest, base_path);
  strlcpy(dest + base_pathlen, uri, pathlen + 1);

  // Return pointer to path, skipping the base
  return dest + base_pathlen;
}

///////////////////////////////////////////////////////////////////////////////
// hello_get_handler
//
// An HTTP GET handler
//

static esp_err_t
hello_get_handler(httpd_req_t *req)
{
  char *buf;
  size_t buf_len;

  // Get header value string length and allocate memory for length + 1,
  // extra byte for null termination
  buf_len = httpd_req_get_hdr_value_len(req, "Host") + 1;
  if (buf_len > 1) {
    buf = (char *) malloc(buf_len);
    // Copy null terminated value string into buffer
    if (httpd_req_get_hdr_value_str(req, "Host", buf, buf_len) == ESP_OK) {
      ESP_LOGD(TAG, "Found header => Host: %s", buf);
    }
    free(buf);
  }

  buf_len = httpd_req_get_hdr_value_len(req, "Test-Header-2") + 1;
  if (buf_len > 1) {
    buf = (char *) malloc(buf_len);
    if (NULL == buf) {
      return ESP_ERR_NO_MEM;
    }
    if (httpd_req_get_hdr_value_str(req, "Test-Header-2", buf, buf_len) == ESP_OK) {
      ESP_LOGD(TAG, "Found header => Test-Header-2: %s", buf);
    }
    free(buf);
  }

  buf_len = httpd_req_get_hdr_value_len(req, "Test-Header-1") + 1;
  if (buf_len > 1) {
    buf = (char *) malloc(buf_len);
    if (httpd_req_get_hdr_value_str(req, "Test-Header-1", buf, buf_len) == ESP_OK) {
      ESP_LOGD(TAG, "Found header => Test-Header-1: %s", buf);
    }
    free(buf);
  }

  // Read URL query string length and allocate memory for length + 1,
  // extra byte for null termination
  buf_len = httpd_req_get_url_query_len(req) + 1;
  if (buf_len > 1) {
    buf = (char *) malloc(buf_len);
    if (NULL == buf) {
      return ESP_ERR_NO_MEM;
    }
    if (httpd_req_get_url_query_str(req, buf, buf_len) == ESP_OK) {
      ESP_LOGD(TAG, "Found URL query => %s", buf);
      char param[32];
      // Get value of expected key from query string
      if (httpd_query_key_value(buf, "query1", param, sizeof(param)) == ESP_OK) {
        ESP_LOGD(TAG, "Found URL query parameter => query1=%s", param);
      }
      if (httpd_query_key_value(buf, "query3", param, sizeof(param)) == ESP_OK) {
        ESP_LOGD(TAG, "Found URL query parameter => query3=%s", param);
      }
      if (httpd_query_key_value(buf, "query2", param, sizeof(param)) == ESP_OK) {
        ESP_LOGD(TAG, "Found URL query parameter => query2=%s", param);
      }
    }
    free(buf);
  }

  // Set some custom headers
  httpd_resp_set_hdr(req, "Custom-Header-1", "Custom-Value-1");
  httpd_resp_set_hdr(req, "Custom-Header-2", "Custom-Value-2");

  // Send response with custom headers and body set as the
  // string passed in user context
  const char *resp_str = "Be Hungry - Stay Foolish!"; //(const char *) req->user_ctx;
  httpd_resp_send(req, resp_str, HTTPD_RESP_USE_STRLEN);

  // After sending the HTTP response the old HTTP request
  // headers are lost. Check if HTTP request headers can be read now.
  if (httpd_req_get_hdr_value_len(req, "Host") == 0) {
    ESP_LOGD(TAG, "Request headers lost");
  }

  return ESP_OK;
}

static const httpd_uri_t hello = { .uri     = "/hello",
                                   .method  = HTTP_GET,
                                   .handler = hello_get_handler,
                                   // Let's pass response string in user
                                   // context to demonstrate it's usage
                                   .user_ctx = "Be Hungry - Stay Foolish!" };

///////////////////////////////////////////////////////////////////////////////
// mainpg_get_handler
//
// Mainpage for web interface
//

static esp_err_t
mainpg_get_handler(httpd_req_t *req)
{
  char *buf;

  char *req_buf;
  size_t req_buf_len;

  buf = (char *) calloc(CHUNK_BUFSIZE, 1);
  if (NULL == buf) {
    return ESP_ERR_NO_MEM;
  }

  // Get application info data
  const esp_app_desc_t *appDescr = esp_app_get_description();

  // Get header value string length and allocate memory for length + 1,
  // extra byte for null termination
  req_buf_len = httpd_req_get_hdr_value_len(req, "Host") + 1;
  if (req_buf_len > 1) {
    req_buf = (char *) malloc(req_buf_len);
    // Copy null terminated value string into buffer
    if (httpd_req_get_hdr_value_str(req, "Host", req_buf, req_buf_len) == ESP_OK) {
      ESP_LOGD(TAG, "Found header => Host: %s", req_buf);
    }
    free(req_buf);
  }

  sprintf(buf, WEBPAGE_START_TEMPLATE, g_persistent.nodeName, "Main Page");
  httpd_resp_send_chunk(req, buf, HTTPD_RESP_USE_STRLEN);

  sprintf(buf,
          "<p><form id=but1 class=\"button\" action='config' method='get'><button>Configuration</button></form></p>");
  httpd_resp_send_chunk(req, buf, HTTPD_RESP_USE_STRLEN);

  sprintf(buf,
          "<p><form id=but2 class=\"button\" action='info' method='get'><button>Node Information</button></form></p>");
  httpd_resp_send_chunk(req, buf, HTTPD_RESP_USE_STRLEN);

    sprintf(buf,
      "<p><form id=but2a class=\"button\" action='canbus' method='get'><button>CAN Bus Console</button></form></p>");
    httpd_resp_send_chunk(req, buf, HTTPD_RESP_USE_STRLEN);

    sprintf(buf,
        "<p><form id=but2b class=\"button\" action='/logs' method='get'><button>Live Logs</button></form></p>");
    httpd_resp_send_chunk(req, buf, HTTPD_RESP_USE_STRLEN);

  sprintf(buf,
          "<p><form id=but3 class=\"button\" action='upgrade' method='get'><button>Firmware "
          "Upgrade</button></form></p>");
  httpd_resp_send_chunk(req, buf, HTTPD_RESP_USE_STRLEN);

  sprintf(buf,
          "<p><form id=but5 class=\"button\" action='reset' method='get'><button name='rst' class='button "
          "bred'>Restart</button></form></p>");
  httpd_resp_send_chunk(req, buf, HTTPD_RESP_USE_STRLEN);

  sprintf(buf, WEBPAGE_END_TEMPLATE_NO_RETURN, web_ui_version(appDescr), g_persistent.nodeName);
  httpd_resp_send_chunk(req, buf, HTTPD_RESP_USE_STRLEN);

  httpd_resp_send_chunk(req, NULL, 0);

  free(buf);

  return ESP_OK;
}

///////////////////////////////////////////////////////////////////////////////
// canbus_get_handler
//
// CAN bus web console using direct device HTTP API
//

static esp_err_t
canbus_get_handler(httpd_req_t *req)
{
  char *buf = (char *) calloc(CHUNK_BUFSIZE, 1);
  if (NULL == buf) {
    return ESP_ERR_NO_MEM;
  }

  const esp_app_desc_t *appDescr = esp_app_get_description();

  sprintf(buf, WEBPAGE_START_TEMPLATE, g_persistent.nodeName, "CAN Bus Console");
  httpd_resp_send_chunk(req, buf, HTTPD_RESP_USE_STRLEN);

  sprintf(buf,
          "<p style='font-size:0.95rem;color:#ddd;'>"
          "Direct device API access to TWAI/CAN. This page sends commands straight to the firmware CAN backend."
          "</p>");
  httpd_resp_send_chunk(req, buf, HTTPD_RESP_USE_STRLEN);

  sprintf(buf,
          "<fieldset><legend>Interface</legend>"
          "<div class='p'>Mode</div><div class='q'>Direct TWAI/CAN API</div><br style='clear:both'>"
          "<div class='p'>Endpoint</div><div class='q'>/canapi</div><br style='clear:both'>"
          "</fieldset>");
  httpd_resp_send_chunk(req, buf, HTTPD_RESP_USE_STRLEN);

  sprintf(buf,
          "<br><fieldset><legend>Send VSCP Event To CAN</legend>"
          "<table style='width:100%%'>"
          "<tr><td>Priority (0-7)</td><td><input id='prio' value='0'></td></tr>"
          "<tr><td>Class</td><td><input id='vclass' value='0'></td></tr>"
          "<tr><td>Type</td><td><input id='vtype' value='1'></td></tr>"
          "<tr><td>Node/Nickname</td><td><input id='nick' value='255'></td></tr>"
      "<tr><td>Data (comma separated)</td><td><input id='data' value='' placeholder='0x01,2,0b00000011'></td></tr>"
          "</table>"
          "<button id='btnSendEvent' type='button' class='bgrn'>Send Event</button>"
          "</fieldset>");
  httpd_resp_send_chunk(req, buf, HTTPD_RESP_USE_STRLEN);

  sprintf(buf,
          "<br><fieldset><legend>CAN Bus Node Discovery</legend>"
          "<table style='width:100%%'>"
          "<tr><td>Who Is There target nickname</td><td><input id='whisNick' value='255'></td></tr>"
          "<tr><td>Scan start nickname</td><td><input id='scanStart' value='1'></td></tr>"
          "<tr><td>Scan end nickname</td><td><input id='scanEnd' value='255'></td></tr>"
      "<tr><td>Serial per-node scan</td><td><input id='scanSerial' type='checkbox' checked></td></tr>"
      "<tr><td>Per-node timeout (ms)</td><td><input id='scanPerNodeMs' value='20'></td></tr>"
          "</table>"
          "<button id='btnWhis' type='button'>Send Who Is There</button><br><br>"
          "<button id='btnScan' type='button'>Run Node Scan</button>"
          "</fieldset>");
  httpd_resp_send_chunk(req, buf, HTTPD_RESP_USE_STRLEN);

  sprintf(buf,
          "<br><fieldset><legend>TWAI Monitor Filters</legend>"
          "<table style='width:100%%'>"
          "<tr><td>CAN ID min (hex)</td><td><input id='filterIdMin' value='0' placeholder='0x0'></td></tr>"
          "<tr><td>CAN ID max (hex)</td><td><input id='filterIdMax' value='FFFFFFFF' placeholder='0xFFFFFFFF'></td></tr>"
          "<tr><td>VSCP Class</td><td><input id='filterClass' value='' placeholder='(empty=all)'></td></tr>"
          "<tr><td>VSCP Type</td><td><input id='filterType' value='' placeholder='(empty=all)'></td></tr>"
          "<tr><td>Node Nickname</td><td><input id='filterNick' value='' placeholder='(empty=all)'></td></tr>"
          "<tr><td>Extended Frames Only</td><td><input id='filterExtd' type='checkbox' checked></td></tr>"
      "<tr><td>Show transmitted frames</td><td><input id='showTxInLog' type='checkbox'></td></tr>"
          "</table>"
          "</fieldset>");
  httpd_resp_send_chunk(req, buf, HTTPD_RESP_USE_STRLEN);

  sprintf(buf,
          "<br><fieldset><legend>API Replies</legend>"
      "<div style='font-size:0.9rem;margin-bottom:6px'>"
      "<span style='color:#66d9ff'>SCAN</span> "
      "<span style='color:#ffd166'>WHO IS THERE</span> "
      "<span style='color:#d6b3ff'>SEND</span> "
      "<span style='color:#ff7b72'>ERROR</span> "
      "<span style='color:#8df186'>TWAI</span>"
      "</div>"
      "<div style='margin-bottom:6px'><button id='btnClearLog' type='button'>Clear Log</button></div>"
      "<div id='log' style='height:260px;overflow:auto;background:#101110;color:#8df186;"
      "font-family:monospace;padding:6px;white-space:pre-wrap;border:1px solid #2f3a2f'></div>"
          "</fieldset>");
  httpd_resp_send_chunk(req, buf, HTTPD_RESP_USE_STRLEN);

  sprintf(buf,
          "<script>"
          "(function(){"
          "function el(id){return document.getElementById(id);}"
      "function parseByteToken(tok){"
      "  var s=(tok||'').trim();"
      "  if(!s.length) return null;"
      "  if(/^0[bB][01]+$/.test(s)){var v=0;for(var i=2;i<s.length;i++){v=(v<<1)+(s.charCodeAt(i)-48);}return (v>=0&&v<=255)?v:null;}"
      "  if(/^0[xX][0-9a-fA-F]+$/.test(s)){var v=parseInt(s.substring(2),16);return (v>=0&&v<=255)?v:null;}"
      "  if(/^0[dD][0-9]+$/.test(s)){var v=parseInt(s.substring(2),10);return (v>=0&&v<=255)?v:null;}"
      "  if(/^[0-9]+$/.test(s)){var v=parseInt(s,10);return (v>=0&&v<=255)?v:null;}"
      "  return null;"
      "}"
      "function hexByte(v){var s=(v&255).toString(16).toUpperCase();return (s.length<2?'0':'')+s;}"
      "function buildTxPreview(){"
      "  var prio=parseInt(el('prio').value.trim(),10);"
      "  var vclass=parseInt(el('vclass').value.trim(),10);"
      "  var vtype=parseInt(el('vtype').value.trim(),10);"
      "  var nick=parseInt(el('nick').value.trim(),10);"
      "  if(!(prio>=0&&prio<=7&&vclass>=0&&vclass<=511&&vtype>=0&&vtype<=255&&nick>=0&&nick<=255)){return null;}"
      "  var raw=el('data').value.trim();"
      "  var parts=[];"
      "  if(raw.length){parts=raw.split(/[\\s,;]+/).filter(function(x){return x.length>0;});}"
      "  if(parts.length>8){return null;}"
      "  var bytes=[];"
      "  for(var i=0;i<parts.length;i++){var b=parseByteToken(parts[i]);if(null===b){return null;}bytes.push(b);}"
      "  var canid=(nick + (vtype<<8) + (vclass<<16) + ((prio&7)<<26))>>>0;"
      "  var data=bytes.map(hexByte).join(':');"
      "  return 'TX: id=0x'+canid.toString(16).toUpperCase()+' prio='+prio+' class='+vclass+' type='+vtype+' nick='+nick+' extd=1 dlc='+bytes.length+' data='+data;"
      "}"
      "function log(s,cls){var t=el('log');if(!t)return;var d=document.createElement('div');"
      "d.textContent=(new Date()).toISOString()+\" \"+s;"
      "if('scan'===cls){d.style.color='#66d9ff';}"
      "else if('whis'===cls){d.style.color='#ffd166';}"
      "else if('error'===cls){d.style.color='#ff7b72';}"
      "else if('twai'===cls){d.style.color='#8df186';}"
      "else if('send'===cls){d.style.color='#d6b3ff';}"
      "t.appendChild(d);t.scrollTop=t.scrollHeight;}"
          "function api(q){fetch('/canapi?'+q,{method:'GET'})"
          "  .then(function(r){return r.text().then(function(t){return {ok:r.ok,status:r.status,text:t};});})"
      "  .then(function(res){"
      "    var cls='';"
      "    if(q.indexOf('cmd=scan')===0) cls='scan';"
      "    else if(q.indexOf('cmd=whis')===0) cls='whis';"
      "    else if(q.indexOf('cmd=send')===0) cls='send';"
      "    if(!res.ok) cls='error';"
      "    log('API '+res.status+' '+res.text,cls);"
      "  })"
      "  .catch(function(e){log('API error '+e,'error');});}"
          "el('btnClearLog').onclick=function(){var t=el('log');if(t){t.textContent='';}};"
          "el('btnSendEvent').onclick=function(){"
          "  if(el('showTxInLog').checked){var preview=buildTxPreview();if(preview){log(preview,'send');}else{log('TX preview unavailable: invalid outgoing frame fields','error');}}"
          "  var q='cmd=send'"
          "    +'&prio='+encodeURIComponent(el('prio').value.trim())"
          "    +'&class='+encodeURIComponent(el('vclass').value.trim())"
          "    +'&type='+encodeURIComponent(el('vtype').value.trim())"
          "    +'&nick='+encodeURIComponent(el('nick').value.trim())"
          "    +'&data='+encodeURIComponent(el('data').value.trim());"
          "  api(q);"
          "};"
          "el('btnWhis').onclick=function(){"
          "  api('cmd=whis&nick='+encodeURIComponent(el('whisNick').value.trim()));"
          "};"
          "el('btnScan').onclick=function(){"
          "  var q='cmd=scan&start='+encodeURIComponent(el('scanStart').value.trim())"
          "    +'&end='+encodeURIComponent(el('scanEnd').value.trim())"
          "    +'&mode='+(el('scanSerial').checked?'serial':'burst')"
          "    +'&pernode_ms='+encodeURIComponent(el('scanPerNodeMs').value.trim());"
          "  api(q);"
          "};"
          "log('Starting TWAI bus monitor - polling for CAN frames...','twai');"
          "var twaiRunning=true;"
          "function twaiMonitor(){"
          "  if(!twaiRunning) return;"
          "  var q='cmd=monitor';"
          "  var idMin=el('filterIdMin').value.trim();"
          "  var idMax=el('filterIdMax').value.trim();"
          "  var cls=el('filterClass').value.trim();"
          "  var typ=el('filterType').value.trim();"
          "  var nick=el('filterNick').value.trim();"
          "  var extdOnly=el('filterExtd').checked;"
          "  if(idMin) q+='&id_min='+encodeURIComponent(idMin);"
          "  if(idMax) q+='&id_max='+encodeURIComponent(idMax);"
          "  if(cls) q+='&class='+encodeURIComponent(cls);"
          "  if(typ) q+='&type='+encodeURIComponent(typ);"
          "  if(nick) q+='&nick='+encodeURIComponent(nick);"
          "  if(extdOnly) q+='&extd_only=1';"
          "  fetch('/canapi?'+q,{method:'GET'})"
          "    .then(function(r){return r.text();})"
          "    .then(function(text){"
          "      if(text && text.length>0){"
          "        var lines=text.split('\\n');"
          "        for(var i=0;i<lines.length;i++){"
          "          if(lines[i].length>0){"
          "            log('TWAI: '+lines[i],'twai');"
          "          }"
          "        }"
          "      }"
          "      setTimeout(twaiMonitor,500);"
          "    })"
          "    .catch(function(e){"
          "      log('TWAI monitor error: '+e,'error');"
          "      setTimeout(twaiMonitor,500);"
          "    });"
          "}"
          "twaiMonitor();"
          "})();"
          "</script>");
  httpd_resp_send_chunk(req, buf, HTTPD_RESP_USE_STRLEN);

  sprintf(buf, WEBPAGE_END_TEMPLATE, web_ui_version(appDescr), g_persistent.nodeName);
  httpd_resp_send_chunk(req, buf, HTTPD_RESP_USE_STRLEN);
  httpd_resp_send_chunk(req, NULL, 0);

  free(buf);
  return ESP_OK;
}

///////////////////////////////////////////////////////////////////////////////
// logs_get_handler
//
// Web page that displays device logs in near real-time.
//

static esp_err_t
logs_get_handler(httpd_req_t *req)
{
  char *buf = (char *) calloc(CHUNK_BUFSIZE, 1);
  if (NULL == buf) {
    return ESP_ERR_NO_MEM;
  }

  const esp_app_desc_t *appDescr = esp_app_get_description();

  sprintf(buf, WEBPAGE_START_TEMPLATE, g_persistent.nodeName, "Live Log Console");
  httpd_resp_send_chunk(req, buf, HTTPD_RESP_USE_STRLEN);

  sprintf(buf,
          "<p style='font-size:0.95rem;color:#ddd;'>"
          "Streaming firmware log output from this node in real time."
          "</p>");
  httpd_resp_send_chunk(req, buf, HTTPD_RESP_USE_STRLEN);

  sprintf(buf,
          "<fieldset><legend>Log Stream</legend>"
          "<div style='display:flex;gap:8px;margin-bottom:8px'>"
          "<button id='btnPause' type='button'>Pause</button>"
          "<button id='btnClear' type='button'>Clear</button>"
          "</div>"
          "<div id='logbox' style='height:360px;overflow:auto;background:#101110;color:#8df186;"
          "font-family:monospace;padding:6px;white-space:pre-wrap;border:1px solid #2f3a2f'></div>"
          "</fieldset>");
  httpd_resp_send_chunk(req, buf, HTTPD_RESP_USE_STRLEN);

  sprintf(buf,
          "<script>"
          "(function(){"
          "var since=0;var paused=false;"
          "function el(id){return document.getElementById(id);}"
          "function addLine(s){var t=el('logbox');if(!t)return;"
          "var d=document.createElement('div');d.textContent=s;t.appendChild(d);"
          "while(t.childNodes.length>800){t.removeChild(t.firstChild);}"
          "t.scrollTop=t.scrollHeight;}"
          "el('btnPause').onclick=function(){paused=!paused;this.textContent=paused?'Resume':'Pause';};"
          "el('btnClear').onclick=function(){var t=el('logbox');if(t){t.textContent='';}};"
          "function poll(){"
          "if(paused){setTimeout(poll,400);return;}"
          "fetch('/logstream?since='+since,{method:'GET'})"
          ".then(function(r){return r.text();})"
          ".then(function(txt){"
          "if(!txt){setTimeout(poll,350);return;}"
          "var lines=txt.split('\\n');"
          "for(var i=0;i<lines.length;i++){"
          "if(lines[i].indexOf('NEXT ')==0){since=parseInt(lines[i].substring(5),10)||since;}"
          "else if(lines[i].length){addLine(lines[i]);}"
          "}"
          "setTimeout(poll,120);"
          "})"
          ".catch(function(e){addLine('logstream error: '+e);setTimeout(poll,700);});"
          "}"
          "poll();"
          "})();"
          "</script>");
  httpd_resp_send_chunk(req, buf, HTTPD_RESP_USE_STRLEN);

  sprintf(buf, WEBPAGE_END_TEMPLATE, web_ui_version(appDescr), g_persistent.nodeName);
  httpd_resp_send_chunk(req, buf, HTTPD_RESP_USE_STRLEN);
  httpd_resp_send_chunk(req, NULL, 0);

  free(buf);
  return ESP_OK;
}

///////////////////////////////////////////////////////////////////////////////
// logstream_get_handler
//

static esp_err_t
logstream_get_handler(httpd_req_t *req)
{
  char qbuf[64] = { 0 };
  char sval[20] = { 0 };
  uint32_t since = 0;

  if ((httpd_req_get_url_query_len(req) > 0) &&
      (ESP_OK == httpd_req_get_url_query_str(req, qbuf, sizeof(qbuf))) &&
      (ESP_OK == httpd_query_key_value(qbuf, "since", sval, sizeof(sval)))) {
    since = (uint32_t) strtoul(sval, NULL, 10);
  }

  httpd_resp_set_type(req, "text/plain; charset=utf-8");
  httpd_resp_set_hdr(req, "Cache-Control", "no-store, no-cache, must-revalidate, max-age=0");
  httpd_resp_set_hdr(req, "Pragma", "no-cache");

  if (NULL == g_web_log_mutex) {
    httpd_resp_sendstr(req, "NEXT 0\n");
    return ESP_OK;
  }

  if (pdTRUE != xSemaphoreTake(g_web_log_mutex, pdMS_TO_TICKS(50))) {
    httpd_resp_sendstr(req, "NEXT 0\n");
    return ESP_OK;
  }

  uint32_t cur = g_web_log_seq;
  uint32_t first_available = (cur > WEB_LOG_RING_SIZE) ? (cur - WEB_LOG_RING_SIZE + 1U) : 1U;
  uint32_t start = since + 1U;
  if (start < first_available) {
    start = first_available;
  }

  char hdr[32] = { 0 };
  snprintf(hdr, sizeof(hdr), "NEXT %lu\n", (unsigned long) cur);
  httpd_resp_send_chunk(req, hdr, HTTPD_RESP_USE_STRLEN);

  for (uint32_t seq = start; seq <= cur; ++seq) {
    size_t idx = (size_t) ((seq - 1U) % WEB_LOG_RING_SIZE);
    if (g_web_log_ring[idx].seq != seq) {
      continue;
    }

    if ('\0' == g_web_log_ring[idx].line[0]) {
      continue;
    }

    httpd_resp_send_chunk(req, g_web_log_ring[idx].line, HTTPD_RESP_USE_STRLEN);
    httpd_resp_send_chunk(req, "\n", 1);
  }

  xSemaphoreGive(g_web_log_mutex);

  httpd_resp_send_chunk(req, NULL, 0);
  return ESP_OK;
}

///////////////////////////////////////////////////////////////////////////////
// canapi helpers
//

static bool
canapi_is_digit_string(const char *s)
{
  if ((NULL == s) || ('\0' == *s)) {
    return false;
  }

  for (const char *p = s; *p; ++p) {
    if ((*p < '0') || (*p > '9')) {
      return false;
    }
  }

  return true;
}

static int
canapi_parse_byte_token(const char *tok, size_t tok_len, uint8_t *val)
{
  char tmp[24] = { 0 };

  if ((NULL == tok) || (NULL == val) || (0 == tok_len) || (tok_len >= sizeof(tmp))) {
    return VSCP_ERROR_INVALID_SYNTAX;
  }

  memcpy(tmp, tok, tok_len);
  tmp[tok_len] = '\0';

  // Accept common byte formats: decimal (42), hex (0x2A), binary (0b101010).
  if ((tok_len > 2) && ('0' == tmp[0]) && (('b' == tmp[1]) || ('B' == tmp[1]))) {
    int v = 0;
    char *p = tmp + 2;
    if ('\0' == *p) {
      return VSCP_ERROR_INVALID_SYNTAX;
    }
    while ('\0' != *p) {
      if (('0' != *p) && ('1' != *p)) {
        return VSCP_ERROR_INVALID_SYNTAX;
      }
      v = (v << 1) + (*p - '0');
      if (v > 255) {
        return VSCP_ERROR_INVALID_SYNTAX;
      }
      p++;
    }
    *val = (uint8_t) v;
    return VSCP_ERROR_SUCCESS;
  }

  char *p = tmp;
  int base = 10;
  if ((tok_len > 2) && ('0' == tmp[0]) && (('x' == tmp[1]) || ('X' == tmp[1]))) {
    p = tmp + 2;
    base = 16;
  }
  else if ((tok_len > 2) && ('0' == tmp[0]) && (('d' == tmp[1]) || ('D' == tmp[1]))) {
    p = tmp + 2;
    base = 10;
  }

  if ('\0' == *p) {
    return VSCP_ERROR_INVALID_SYNTAX;
  }

  char *endptr = NULL;
  long v = strtol(p, &endptr, base);
  if ((NULL == endptr) || ('\0' != *endptr) || (v < 0) || (v > 255)) {
    return VSCP_ERROR_INVALID_SYNTAX;
  }

  *val = (uint8_t) v;
  return VSCP_ERROR_SUCCESS;
}

static int
canapi_parse_data_list(const char *src, uint8_t *dst, uint8_t *len)
{
  size_t n = 0;
  const char *p = src;

  if ((NULL == src) || (NULL == dst) || (NULL == len)) {
    return VSCP_ERROR_INVALID_POINTER;
  }

  *len = 0;

  while (*p) {
    while (*p && ((' ' == *p) || (',' == *p) || (';' == *p) || ('\t' == *p) || ('\r' == *p) || ('\n' == *p))) {
      p++;
    }

    if (!*p) {
      break;
    }

    const char *tok = p;
    while (*p && !(' ' == *p || ',' == *p || ';' == *p || '\t' == *p || '\r' == *p || '\n' == *p)) {
      p++;
    }
    size_t tok_len = (size_t) (p - tok);

    if (n >= 8) {
      return VSCP_ERROR_INVALID_SYNTAX;
    }

    if (VSCP_ERROR_SUCCESS != canapi_parse_byte_token(tok, tok_len, &dst[n])) {
      return VSCP_ERROR_INVALID_SYNTAX;
    }
    n++;
  }

  *len = (uint8_t) n;
  return VSCP_ERROR_SUCCESS;
}

static esp_err_t
canapi_send_vscp_as_can(uint8_t prio,
                        uint16_t vscp_class,
                        uint8_t vscp_type,
                        uint8_t nickname,
                        const uint8_t *pdata,
                        uint8_t sizeData)
{
  can4vscp_frame_t msg = { 0 };
  msg.identifier        = (uint32_t) nickname + (((uint32_t) vscp_type) << 8) + (((uint32_t) vscp_class) << 16) +
                   ((((uint32_t) prio) & 0x07u) << 26);
  msg.extd             = 1;
  msg.rtr              = 0;
  msg.data_length_code = sizeData;
  if ((sizeData > 0) && (NULL != pdata)) {
    memcpy(msg.data, pdata, sizeData);
  }
  return can4vscp_send(&msg, pdMS_TO_TICKS(100));
}

static void
canapi_decode_can4vscp_identifier(uint32_t identifier, uint8_t *prio, uint16_t *vscp_class, uint8_t *vscp_type, uint8_t *nickname)
{
  if (NULL != prio) {
    *prio = (uint8_t) ((identifier >> 26) & 0x07u);
  }

  if (NULL != vscp_class) {
    *vscp_class = (uint16_t) ((identifier >> 16) & 0x01ffu);
  }

  if (NULL != vscp_type) {
    *vscp_type = (uint8_t) ((identifier >> 8) & 0xffu);
  }

  if (NULL != nickname) {
    *nickname = (uint8_t) (identifier & 0xffu);
  }
}

static void
canapi_reset_reply_queue(void)
{
  if (NULL == tr_canapi.fromcan_queue) {
    return;
  }

  can4vscp_frame_t rxmsg = { 0 };
  while (pdPASS == xQueueReceive(tr_canapi.fromcan_queue, &rxmsg, 0)) {
    ;
  }
}

static size_t
canapi_append_nick_list(char *dst, size_t dst_len, const bool *seen)
{
  size_t used = 0;

  if ((NULL == dst) || (0 == dst_len) || (NULL == seen)) {
    return 0;
  }

  for (uint16_t nick = 0; nick < 256; ++nick) {
    if (!seen[nick]) {
      continue;
    }

    int n;
    if (used > 0) {
      n = snprintf(dst + used, dst_len - used, ",%u", (unsigned int) nick);
    }
    else {
      n = snprintf(dst + used, dst_len - used, "%u", (unsigned int) nick);
    }

    if ((n <= 0) || ((size_t) n >= (dst_len - used))) {
      break;
    }

    used += (size_t) n;
  }

  return used;
}

///////////////////////////////////////////////////////////////////////////////
// canapi_get_handler
//
// Direct HTTP API for CAN operations
//

static esp_err_t
canapi_get_handler(httpd_req_t *req)
{
  char qbuf[256]  = { 0 };
  char cmd[16]    = { 0 };
  char param[128] = { 0 };

  httpd_resp_set_type(req, "text/plain");

  size_t qlen = httpd_req_get_url_query_len(req) + 1;
  if (qlen <= 1 || qlen > sizeof(qbuf)) {
    httpd_resp_set_status(req, "400 Bad Request");
    httpd_resp_sendstr(req, "ERR: missing query");
    return ESP_OK;
  }

  if (ESP_OK != httpd_req_get_url_query_str(req, qbuf, sizeof(qbuf))) {
    httpd_resp_set_status(req, "400 Bad Request");
    httpd_resp_sendstr(req, "ERR: invalid query");
    return ESP_OK;
  }

  if (ESP_OK != httpd_query_key_value(qbuf, "cmd", cmd, sizeof(cmd))) {
    httpd_resp_set_status(req, "400 Bad Request");
    httpd_resp_sendstr(req, "ERR: missing cmd");
    return ESP_OK;
  }

  for (char *p = cmd; *p; ++p) {
    *p = (char) tolower((unsigned char) *p);
  }

  if (0 == strcmp(cmd, "send")) {
    uint8_t prio;
    uint8_t vtype;
    uint8_t nick;
    uint16_t vclass;
    uint8_t frame_data[8] = { 0 };
    uint8_t frame_data_len = 0;
    char *decoded_data = NULL;

    if ((ESP_OK != httpd_query_key_value(qbuf, "prio", param, sizeof(param))) || !canapi_is_digit_string(param)) {
      httpd_resp_set_status(req, "400 Bad Request");
      httpd_resp_sendstr(req, "ERR: invalid prio");
      return ESP_OK;
    }
    long l = strtol(param, NULL, 10);
    if ((l < 0) || (l > 7)) {
      httpd_resp_set_status(req, "400 Bad Request");
      httpd_resp_sendstr(req, "ERR: prio out of range");
      return ESP_OK;
    }
    prio = (uint8_t) l;

    if ((ESP_OK != httpd_query_key_value(qbuf, "class", param, sizeof(param))) || !canapi_is_digit_string(param)) {
      httpd_resp_set_status(req, "400 Bad Request");
      httpd_resp_sendstr(req, "ERR: invalid class");
      return ESP_OK;
    }
    l = strtol(param, NULL, 10);
    if ((l < 0) || (l > 511)) {
      httpd_resp_set_status(req, "400 Bad Request");
      httpd_resp_sendstr(req, "ERR: class out of range");
      return ESP_OK;
    }
    vclass = (uint16_t) l;

    if ((ESP_OK != httpd_query_key_value(qbuf, "type", param, sizeof(param))) || !canapi_is_digit_string(param)) {
      httpd_resp_set_status(req, "400 Bad Request");
      httpd_resp_sendstr(req, "ERR: invalid type");
      return ESP_OK;
    }
    l = strtol(param, NULL, 10);
    if ((l < 0) || (l > 255)) {
      httpd_resp_set_status(req, "400 Bad Request");
      httpd_resp_sendstr(req, "ERR: type out of range");
      return ESP_OK;
    }
    vtype = (uint8_t) l;

    if ((ESP_OK != httpd_query_key_value(qbuf, "nick", param, sizeof(param))) || !canapi_is_digit_string(param)) {
      httpd_resp_set_status(req, "400 Bad Request");
      httpd_resp_sendstr(req, "ERR: invalid nick");
      return ESP_OK;
    }
    l = strtol(param, NULL, 10);
    if ((l < 0) || (l > 255)) {
      httpd_resp_set_status(req, "400 Bad Request");
      httpd_resp_sendstr(req, "ERR: nick out of range");
      return ESP_OK;
    }
    nick = (uint8_t) l;

    if (ESP_OK == httpd_query_key_value(qbuf, "data", param, sizeof(param))) {
      decoded_data = urlDecode(param);
      const char *datastr = (NULL != decoded_data) ? decoded_data : param;
      if (VSCP_ERROR_SUCCESS != canapi_parse_data_list(datastr, frame_data, &frame_data_len)) {
        if (NULL != decoded_data) {
          free(decoded_data);
        }
        httpd_resp_set_status(req, "400 Bad Request");
        httpd_resp_sendstr(req, "ERR: invalid data");
        return ESP_OK;
      }
    }

    // Push frame to TX queue — twai_transmit_task will call can4vscp_send.
    // This returns immediately without blocking the HTTP task on CAN bus TX.
    can4vscp_frame_t tx_frame = { 0 };
    tx_frame.identifier       = (uint32_t) nick +
                                ((uint32_t) vtype << 8) +
                                ((uint32_t) vclass << 16) +
                                (((uint32_t) prio & 0x07u) << 26);
    tx_frame.extd             = 1;
    tx_frame.rtr              = 0;
    tx_frame.data_length_code = frame_data_len;
    if (frame_data_len > 0) {
      memcpy(tx_frame.data, frame_data, frame_data_len);
    }

    if ((NULL == tr_canapi.tocan_queue) ||
      (pdPASS != xQueueSendToBack(tr_canapi.tocan_queue, &tx_frame, pdMS_TO_TICKS(10)))) {
      if (NULL != decoded_data) {
        free(decoded_data);
      }
      httpd_resp_set_status(req, "500 Internal Server Error");
      httpd_resp_sendstr(req, "ERR: CAN TX queue full");
      return ESP_OK;
    }

    if (NULL != decoded_data) {
      free(decoded_data);
    }

    char rsp[64] = { 0 };
    snprintf(rsp, sizeof(rsp), "OK: SENDEVENT dlc=%u", (unsigned int) frame_data_len);
    httpd_resp_sendstr(req, rsp);
    return ESP_OK;
  }
  else if (0 == strcmp(cmd, "whis")) {
    uint8_t nick = 255;
    bool seen[256] = { 0 };
    uint16_t replies = 0;

    if (ESP_OK == httpd_query_key_value(qbuf, "nick", param, sizeof(param))) {
      if (!canapi_is_digit_string(param)) {
        httpd_resp_set_status(req, "400 Bad Request");
        httpd_resp_sendstr(req, "ERR: invalid nick");
        return ESP_OK;
      }
      long l = strtol(param, NULL, 10);
      if ((l < 0) || (l > 255)) {
        httpd_resp_set_status(req, "400 Bad Request");
        httpd_resp_sendstr(req, "ERR: nick out of range");
        return ESP_OK;
      }
      nick = (uint8_t) l;
    }

    if (NULL == tr_canapi.fromcan_queue) {
      httpd_resp_set_status(req, "500 Internal Server Error");
      httpd_resp_sendstr(req, "ERR: CAN reply queue unavailable");
      return ESP_OK;
    }

    canapi_reset_reply_queue();

    uint8_t data[1] = { nick };
    if (ESP_OK != canapi_send_vscp_as_can(0,
                                          VSCP_CLASS1_PROTOCOL,
                                          VSCP_TYPE_PROTOCOL_WHO_IS_THERE,
                                          0,
                                          data,
                                          sizeof(data))) {
      httpd_resp_set_status(req, "500 Internal Server Error");
      httpd_resp_sendstr(req, "ERR: Who Is There send failed");
      return ESP_OK;
    }

    int64_t deadline = esp_timer_get_time() + (int64_t) (1500 * 1000);
    while (esp_timer_get_time() < deadline) {
      can4vscp_frame_t rxmsg = { 0 };
      if (pdPASS != xQueueReceive(tr_canapi.fromcan_queue, &rxmsg, pdMS_TO_TICKS(50))) {
        continue;
      }

      if (!rxmsg.extd) {
        continue;
      }

      uint16_t rx_class = 0;
      uint8_t rx_type = 0;
      uint8_t src_nick = 0;
      canapi_decode_can4vscp_identifier(rxmsg.identifier, NULL, &rx_class, &rx_type, &src_nick);

      if ((VSCP_CLASS1_PROTOCOL == rx_class) && (VSCP_TYPE_PROTOCOL_WHO_IS_THERE_RESPONSE == rx_type)) {
        if (!seen[src_nick]) {
          seen[src_nick] = true;
          replies++;
        }
      }
    }

    char node_list[700] = { 0 };
    canapi_append_nick_list(node_list, sizeof(node_list), seen);

    char rsp[900] = { 0 };
    snprintf(rsp,
             sizeof(rsp),
             "OK: Who Is There target=%u replies=%u nodes=%s",
             (unsigned int) nick,
             (unsigned int) replies,
             (0 == node_list[0]) ? "-" : node_list);
    httpd_resp_sendstr(req, rsp);
    return ESP_OK;
  }
  else if (0 == strcmp(cmd, "scan")) {
    uint8_t start_nick = 1;
    uint8_t end_nick   = 255;
    uint16_t pernode_ms = 20;
    bool serial_mode = true;
    bool seen[256] = { 0 };

    if (ESP_OK == httpd_query_key_value(qbuf, "start", param, sizeof(param))) {
      if (!canapi_is_digit_string(param)) {
        httpd_resp_set_status(req, "400 Bad Request");
        httpd_resp_sendstr(req, "ERR: invalid start");
        return ESP_OK;
      }
      long l = strtol(param, NULL, 10);
      if ((l < 0) || (l > 255)) {
        httpd_resp_set_status(req, "400 Bad Request");
        httpd_resp_sendstr(req, "ERR: start out of range");
        return ESP_OK;
      }
      start_nick = (uint8_t) l;
    }

    if (ESP_OK == httpd_query_key_value(qbuf, "end", param, sizeof(param))) {
      if (!canapi_is_digit_string(param)) {
        httpd_resp_set_status(req, "400 Bad Request");
        httpd_resp_sendstr(req, "ERR: invalid end");
        return ESP_OK;
      }
      long l = strtol(param, NULL, 10);
      if ((l < 0) || (l > 255)) {
        httpd_resp_set_status(req, "400 Bad Request");
        httpd_resp_sendstr(req, "ERR: end out of range");
        return ESP_OK;
      }
      end_nick = (uint8_t) l;
    }

    if (start_nick > end_nick) {
      httpd_resp_set_status(req, "400 Bad Request");
      httpd_resp_sendstr(req, "ERR: invalid range");
      return ESP_OK;
    }

    if (ESP_OK == httpd_query_key_value(qbuf, "mode", param, sizeof(param))) {
      for (char *p = param; *p; ++p) {
        *p = (char) tolower((unsigned char) *p);
      }

      if (0 == strcmp(param, "serial")) {
        serial_mode = true;
      }
      else if (0 == strcmp(param, "burst")) {
        serial_mode = false;
      }
      else {
        httpd_resp_set_status(req, "400 Bad Request");
        httpd_resp_sendstr(req, "ERR: invalid mode");
        return ESP_OK;
      }
    }

    if (ESP_OK == httpd_query_key_value(qbuf, "pernode_ms", param, sizeof(param))) {
      if (!canapi_is_digit_string(param)) {
        httpd_resp_set_status(req, "400 Bad Request");
        httpd_resp_sendstr(req, "ERR: invalid pernode_ms");
        return ESP_OK;
      }

      long l = strtol(param, NULL, 10);
      if ((l < 1) || (l > 2000)) {
        httpd_resp_set_status(req, "400 Bad Request");
        httpd_resp_sendstr(req, "ERR: pernode_ms out of range");
        return ESP_OK;
      }
      pernode_ms = (uint16_t) l;
    }

    if (NULL == tr_canapi.fromcan_queue) {
      httpd_resp_set_status(req, "500 Internal Server Error");
      httpd_resp_sendstr(req, "ERR: CAN reply queue unavailable");
      return ESP_OK;
    }

    canapi_reset_reply_queue();

    ESP_LOGI(TAG, "SCAN: Started (serial_mode=%u, pernode_ms=%u, range=%u-%u)",
             serial_mode, pernode_ms, start_nick, end_nick);

    uint16_t sent = 0;
    uint16_t fail = 0;
    uint16_t replies = 0;

    for (uint16_t nick = start_nick; nick <= end_nick; ++nick) {
      uint8_t data[2] = { (uint8_t) nick, VSCP_STD_REGISTER_GUID };
      if (ESP_OK == canapi_send_vscp_as_can(0,
                                            VSCP_CLASS1_PROTOCOL,
                                            VSCP_TYPE_PROTOCOL_READ_REGISTER,
                                            0,
                                            data,
                                            sizeof(data))) {
        sent++;
        ESP_LOGD(TAG, "SCAN: Sent READ_REGISTER 0x%02X to node %u", VSCP_STD_REGISTER_GUID, nick);
      }
      else {
        fail++;
        ESP_LOGW(TAG, "SCAN: Failed to send READ_REGISTER to node %u", nick);
        continue;
      }

      if (!serial_mode) {
        vTaskDelay(pdMS_TO_TICKS(2));
        continue;
      }

      int64_t pernode_deadline = esp_timer_get_time() + ((int64_t) pernode_ms * 1000);
      while (esp_timer_get_time() < pernode_deadline) {
        can4vscp_frame_t rxmsg = { 0 };
        if (pdPASS != xQueueReceive(tr_canapi.fromcan_queue, &rxmsg, pdMS_TO_TICKS(5))) {
          continue;
        }

        ESP_LOGI(TAG, "SCAN serial mode: Received frame id=0x%lX, extd=%u, dlc=%u, data[0]=0x%02X, data[1]=0x%02X",
                 rxmsg.identifier, rxmsg.extd, rxmsg.data_length_code, rxmsg.data[0], rxmsg.data[1]);

        if (!rxmsg.extd) {
          ESP_LOGD(TAG, "SCAN serial mode: Skipping non-extended frame");
          continue;
        }

        uint16_t rx_class = 0;
        uint8_t rx_type = 0;
        uint8_t src_nick = 0;
        canapi_decode_can4vscp_identifier(rxmsg.identifier, NULL, &rx_class, &rx_type, &src_nick);

        ESP_LOGI(TAG, "SCAN serial mode: Decoded - src_nick=%u, type=%u, class=%u, target_nick=%u",
                 src_nick, rx_type, rx_class, (unsigned int) nick);

        if ((VSCP_CLASS1_PROTOCOL == rx_class) &&
            (VSCP_TYPE_PROTOCOL_RW_RESPONSE == rx_type) &&
            (rxmsg.data_length_code >= 2) &&
            (VSCP_STD_REGISTER_GUID == rxmsg.data[0]) &&
            (src_nick >= start_nick) &&
            (src_nick <= end_nick)) {
          ESP_LOGI(TAG, "SCAN serial mode: Found node %u", src_nick);
          if (!seen[src_nick]) {
            seen[src_nick] = true;
            replies++;
          }

          if (src_nick == (uint8_t) nick) {
            break;
          }
        } else {
          ESP_LOGW(TAG, "SCAN serial mode: Frame didn't match criteria (class=%u!=0, type=%u!=10, dlc=%u, data[0]=0x%02X!=0x%02X, src_nick=%u in [%u,%u])",
                   rx_class, rx_type, rxmsg.data_length_code, rxmsg.data[0], VSCP_STD_REGISTER_GUID, src_nick, start_nick, end_nick);
        }
      }
    }

    if (!serial_mode) {
      int64_t deadline = esp_timer_get_time() + (int64_t) (2000 * 1000);
      while (esp_timer_get_time() < deadline) {
        can4vscp_frame_t rxmsg = { 0 };
        if (pdPASS != xQueueReceive(tr_canapi.fromcan_queue, &rxmsg, pdMS_TO_TICKS(50))) {
          continue;
        }

        ESP_LOGI(TAG, "SCAN burst mode: Received frame id=0x%lX, extd=%u, dlc=%u, data[0]=0x%02X",
                 rxmsg.identifier, rxmsg.extd, rxmsg.data_length_code, rxmsg.data[0]);

        if (!rxmsg.extd) {
          ESP_LOGD(TAG, "SCAN burst mode: Skipping non-extended frame");
          continue;
        }

        uint16_t rx_class = 0;
        uint8_t rx_type = 0;
        uint8_t src_nick = 0;
        canapi_decode_can4vscp_identifier(rxmsg.identifier, NULL, &rx_class, &rx_type, &src_nick);

        ESP_LOGI(TAG, "SCAN burst mode: Decoded - src_nick=%u, type=%u, class=%u",
                 src_nick, rx_type, rx_class);

        if ((VSCP_CLASS1_PROTOCOL == rx_class) &&
            (VSCP_TYPE_PROTOCOL_RW_RESPONSE == rx_type) &&
            (rxmsg.data_length_code >= 2) &&
            (VSCP_STD_REGISTER_GUID == rxmsg.data[0]) &&
            (src_nick >= start_nick) &&
            (src_nick <= end_nick)) {
          ESP_LOGI(TAG, "SCAN burst mode: Found node %u", src_nick);
          if (!seen[src_nick]) {
            seen[src_nick] = true;
            replies++;
          }
        }
      }
    }

    char node_list[700] = { 0 };
    canapi_append_nick_list(node_list, sizeof(node_list), seen);

    char rsp[950] = { 0 };
    snprintf(rsp,
             sizeof(rsp),
             "OK: SCAN mode=%s pernode_ms=%u reg=0x%02X range=%u-%u sent=%u failed=%u replies=%u nodes=%s",
             serial_mode ? "serial" : "burst",
             (unsigned int) pernode_ms,
             (unsigned int) VSCP_STD_REGISTER_GUID,
             (unsigned int) start_nick,
             (unsigned int) end_nick,
             (unsigned int) sent,
             (unsigned int) fail,
             (unsigned int) replies,
             (0 == node_list[0]) ? "-" : node_list);
    httpd_resp_sendstr(req, rsp);
    return ESP_OK;
  }
  else if (0 == strcmp(cmd, "monitor")) {
    // Return raw TWAI frames from the input queue with optional filtering
    // Parse filter parameters from query string — reuse the already-populated qbuf.
    
    // Default filter values (no filtering)
    uint32_t id_min = 0;
    uint32_t id_max = 0xFFFFFFFFu;
    uint16_t filter_class = 0;  // 0 = any
    uint8_t filter_type = 0;    // 0 = any
    uint8_t filter_nick = 0;    // 0 = any
    bool filter_extd_only = false;
    
    // Parse individual parameters
    char param_val[32] = { 0 };
    
    // Parse id_min (hex)
    if (httpd_query_key_value(qbuf, "id_min", param_val, sizeof(param_val)) == ESP_OK) {
      id_min = strtoul(param_val, NULL, 16);
    }
    
    // Parse id_max (hex)
    memset(param_val, 0, sizeof(param_val));
    if (httpd_query_key_value(qbuf, "id_max", param_val, sizeof(param_val)) == ESP_OK) {
      id_max = strtoul(param_val, NULL, 16);
    }
    
    // Parse class (decimal)
    memset(param_val, 0, sizeof(param_val));
    if (httpd_query_key_value(qbuf, "class", param_val, sizeof(param_val)) == ESP_OK) {
      filter_class = (uint16_t) strtoul(param_val, NULL, 10);
    }
    
    // Parse type (decimal)
    memset(param_val, 0, sizeof(param_val));
    if (httpd_query_key_value(qbuf, "type", param_val, sizeof(param_val)) == ESP_OK) {
      filter_type = (uint8_t) strtoul(param_val, NULL, 10);
    }
    
    // Parse nickname (decimal)
    memset(param_val, 0, sizeof(param_val));
    if (httpd_query_key_value(qbuf, "nick", param_val, sizeof(param_val)) == ESP_OK) {
      filter_nick = (uint8_t) strtoul(param_val, NULL, 10);
    }
    
    // Parse extd_only (presence = true)
    memset(param_val, 0, sizeof(param_val));
    if (httpd_query_key_value(qbuf, "extd_only", param_val, sizeof(param_val)) == ESP_OK) {
      filter_extd_only = true;
    }
    
    // Heap-allocate to avoid overflowing the httpd task stack.
    // NOTE: use a named constant — sizeof(buf) on a pointer gives pointer size (4),
    //       not the allocation size, which was the original cause of heap corruption.
    #define MONITOR_BUFSIZE 2048
    char *buf = (char *) calloc(MONITOR_BUFSIZE, 1);
    if (NULL == buf) {
      httpd_resp_set_status(req, "500 Internal Server Error");
      httpd_resp_sendstr(req, "ERR: out of memory");
      return ESP_OK;
    }
    size_t offset = 0;
    can4vscp_frame_t rxmsg = { 0 };

    // Drain frames from the dedicated monitor queue (filled by twai_receive_task)
    while ((offset < MONITOR_BUFSIZE - 256) && (NULL != tr_monitor.fromcan_queue) &&
           (pdPASS == xQueueReceive(tr_monitor.fromcan_queue, &rxmsg, 0))) {
      
      // Decode identifier
      uint8_t prio = (uint8_t) ((rxmsg.identifier >> 26) & 0x07u);
      uint16_t vscp_class = (uint16_t) ((rxmsg.identifier >> 16) & 0x01ffu);
      uint8_t vscp_type = (uint8_t) ((rxmsg.identifier >> 8) & 0xffu);
      uint8_t nickname = (uint8_t) (rxmsg.identifier & 0xffu);
      
      // Apply filters
      if (rxmsg.identifier < id_min || rxmsg.identifier > id_max) {
        continue;  // Outside CAN ID range
      }
      if (filter_extd_only && !rxmsg.extd) {
        continue;  // Not extended frame but extended-only filter active
      }
      if (filter_class != 0 && vscp_class != filter_class) {
        continue;  // Class mismatch
      }
      if (filter_type != 0 && vscp_type != filter_type) {
        continue;  // Type mismatch
      }
      if (filter_nick != 0 && nickname != filter_nick) {
        continue;  // Nickname mismatch
      }
      
      // Frame passes all filters - add to output
      int line_len = snprintf(buf + offset, MONITOR_BUFSIZE - offset,
                              "id=0x%lX prio=%u class=%u type=%u nick=%u extd=%u dlc=%u data=",
                              rxmsg.identifier, prio, vscp_class, vscp_type, nickname,
                              rxmsg.extd, rxmsg.data_length_code);
      if (line_len < 0) break;
      offset += (size_t) line_len;

      // Append data bytes
      for (int i = 0; i < rxmsg.data_length_code && i < 8; i++) {
        line_len = snprintf(buf + offset, MONITOR_BUFSIZE - offset, "%02X", rxmsg.data[i]);
        if (line_len < 0) break;
        offset += (size_t) line_len;
        if (i < rxmsg.data_length_code - 1) {
          buf[offset++] = ':';
        }
      }
      buf[offset++] = '\n';
      #undef MONITOR_BUFSIZE
    }

    if (offset > 0) {
      httpd_resp_send(req, buf, offset);
    } else {
      httpd_resp_sendstr(req, "");
    }
    free(buf);
    return ESP_OK;
  }

  httpd_resp_set_status(req, "400 Bad Request");
  httpd_resp_sendstr(req, "ERR: unknown cmd");
  return ESP_OK;
}

// static const httpd_uri_t mainpg = { .uri     = "/index.html",
//                                    .method  = HTTP_GET,
//                                    .handler = mainpg_get_handler,
//                                    .user_ctx = NULL };

///////////////////////////////////////////////////////////////////////////////
// config_get_handler
//

static esp_err_t
config_get_handler(httpd_req_t *req)
{
  // esp_err_t rv;
  char *buf;
  // char *temp;

  char *req_buf;
  size_t req_buf_len;

  buf = (char *) calloc(CHUNK_BUFSIZE, 1);
  if (NULL == buf) {
    return ESP_ERR_NO_MEM;
  }

  // Get application info data
  const esp_app_desc_t *appDescr = esp_app_get_description();

  // Get header value string length and allocate memory for length + 1,
  // extra byte for null termination
  req_buf_len = httpd_req_get_hdr_value_len(req, "Host") + 1;
  if (req_buf_len > 1) {
    req_buf = (char *) malloc(req_buf_len);
    // Copy null terminated value string into buffer
    if (httpd_req_get_hdr_value_str(req, "Host", req_buf, req_buf_len) == ESP_OK) {
      ESP_LOGD(TAG, "Found header => Host: %s", req_buf);
    }
    free(req_buf);
  }

  sprintf(buf, WEBPAGE_START_TEMPLATE, g_persistent.nodeName, "Configuration");
  httpd_resp_send_chunk(req, buf, HTTPD_RESP_USE_STRLEN);

  sprintf(buf, "<p><form id=but1 class=\"button\" action='cfgmodule' method='get'><button>Module</button></form></p>");
  httpd_resp_send_chunk(req, buf, HTTPD_RESP_USE_STRLEN);

  sprintf(buf, "<p><form id=but2 class=\"button\" action='cfgwifi' method='get'><button>WiFi</button></form></p>");
  httpd_resp_send_chunk(req, buf, HTTPD_RESP_USE_STRLEN);

  sprintf(buf, "<p><form id=but3 class=\"button\" action='cfgcan' method='get'><button>CAN/TWAI</button></form></p>");
  httpd_resp_send_chunk(req, buf, HTTPD_RESP_USE_STRLEN);

  sprintf(buf,
          "<p><form id=but3 class=\"button\" action='cfgweb' method='get'><button>Web interface</button></form></p>");
  httpd_resp_send_chunk(req, buf, HTTPD_RESP_USE_STRLEN);

  sprintf(
    buf,
    "<p><form id=but3 class=\"button\" action='cfgvscplink' method='get'><button>VSCP Link Srv</button></form></p>");
  httpd_resp_send_chunk(req, buf, HTTPD_RESP_USE_STRLEN);

  sprintf(buf, "<p><form id=but3 class=\"button\" action='cfgmqtt' method='get'><button>MQTT</button></form></p>");
  httpd_resp_send_chunk(req, buf, HTTPD_RESP_USE_STRLEN);

  sprintf(buf,
          "<p><form id=but3 class=\"button\" action='cfgmulticast' method='get'><button>Multicast</button></form></p>");
  httpd_resp_send_chunk(req, buf, HTTPD_RESP_USE_STRLEN);

  sprintf(buf, "<p><form id=but3 class=\"button\" action='cfgudp' method='get'><button>UDP</button></form></p>");
  httpd_resp_send_chunk(req, buf, HTTPD_RESP_USE_STRLEN);

  sprintf(
    buf,
    "<p><form id=but3 class=\"button\" action='cfgwebsockets' method='get'><button>Websockets</button></form></p>");
  httpd_resp_send_chunk(req, buf, HTTPD_RESP_USE_STRLEN);

  sprintf(buf, "<p><form id=but3 class=\"button\" action='cfglog' method='get'><button>Logging</button></form></p>");
  httpd_resp_send_chunk(req, buf, HTTPD_RESP_USE_STRLEN);

  sprintf(
    buf,
    "<hr /><p><form id=but4 class=\"button\" action='cfgfactorydefaults' method='get'><button name='rst' class='button "
    "bred'>Set factory Defaults</button></form></p>");
  httpd_resp_send_chunk(req, buf, HTTPD_RESP_USE_STRLEN);
  sprintf(buf,
          "<p><form id=but3 class=\"button\" action='cfgbackup' method='get'><button class='button "
          "bgrn'>Backup</button></form></p>");
  httpd_resp_send_chunk(req, buf, HTTPD_RESP_USE_STRLEN);
  sprintf(buf,
          "<p><form id=but3 class=\"button\" action='cfgrestore' method='get'><button class='button "
          "bgrn'>Restore</button></form></p>");
  httpd_resp_send_chunk(req, buf, HTTPD_RESP_USE_STRLEN);

  sprintf(buf, WEBPAGE_END_TEMPLATE, web_ui_version(appDescr), g_persistent.nodeName);
  httpd_resp_send_chunk(req, buf, HTTPD_RESP_USE_STRLEN);

  httpd_resp_send_chunk(req, NULL, 0);

  free(buf);

  return ESP_OK;
}

///////////////////////////////////////////////////////////////////////////////
// config_backup_get_handler
//

static esp_err_t
config_backup_get_handler(httpd_req_t *req)
{
  cJSON *root = cJSON_CreateObject();
  if (NULL == root) {
    httpd_resp_send_err(req, HTTPD_500_INTERNAL_SERVER_ERROR, "Unable to create backup JSON");
    return ESP_FAIL;
  }

  cJSON *persistent = cJSON_AddObjectToObject(root, "persistent");
  if (NULL == persistent) {
    cJSON_Delete(root);
    httpd_resp_send_err(req, HTTPD_500_INTERNAL_SERVER_ERROR, "Unable to create backup object");
    return ESP_FAIL;
  }

  cJSON_AddStringToObject(persistent, "nodeName", g_persistent.nodeName);
  cJSON_AddNumberToObject(persistent, "nodeZone", g_persistent.nodeZone);
  cJSON_AddNumberToObject(persistent, "nodeSubzone", g_persistent.nodeSubzone);
  backup_add_hex_field(persistent, "guid", g_persistent.guid, sizeof(g_persistent.guid));
  cJSON_AddNumberToObject(persistent, "encryptLvl", g_persistent.encryptLvl);
  backup_add_encrypted_blob_field(persistent, "pmk", g_persistent.pmk, sizeof(g_persistent.pmk));
  cJSON_AddNumberToObject(persistent, "pmkLen", g_persistent.pmkLen);
  cJSON_AddNumberToObject(persistent, "bootCnt", g_persistent.bootCnt);

  cJSON_AddNumberToObject(persistent, "canMode", g_persistent.canMode);
  cJSON_AddNumberToObject(persistent, "canSpeed", g_persistent.canSpeed);
  cJSON_AddNumberToObject(persistent, "nSent", g_persistent.nSent);
  cJSON_AddNumberToObject(persistent, "nRecv", g_persistent.nRecv);
  cJSON_AddNumberToObject(persistent, "nErr", g_persistent.nErr);
  cJSON_AddNumberToObject(persistent, "lastError", g_persistent.lastError);
  cJSON_AddNumberToObject(persistent, "canFilter", g_persistent.canFilter);
  cJSON_AddNumberToObject(persistent, "bRawCan", g_persistent.bRawCan);

  cJSON_AddNumberToObject(persistent, "logType", g_persistent.logType);
  cJSON_AddNumberToObject(persistent, "logLevel", g_persistent.logLevel);
  cJSON_AddNumberToObject(persistent, "logRetries", g_persistent.logRetries);
  cJSON_AddNumberToObject(persistent, "logPort", g_persistent.logPort);
  cJSON_AddStringToObject(persistent, "logUrl", g_persistent.logUrl);
  cJSON_AddStringToObject(persistent, "logMqttTopic", g_persistent.logMqttTopic);
  cJSON_AddNumberToObject(persistent, "enableMqttLog", g_persistent.enableMqttLog);

  cJSON_AddStringToObject(persistent, "wifiPrimarySsid", g_persistent.wifiPrimarySsid);
  backup_add_encrypted_str_field(persistent, "wifiPrimaryPassword", g_persistent.wifiPrimaryPassword);
  cJSON_AddStringToObject(persistent, "wifiSecondarySsid", g_persistent.wifiSecondarySsid);
  backup_add_encrypted_str_field(persistent, "wifiSecondaryPassword", g_persistent.wifiSecondaryPassword);
  cJSON_AddNumberToObject(persistent, "wifiStaticEnable", g_persistent.wifiStaticEnable);
  cJSON_AddStringToObject(persistent, "wifiStaticIp", g_persistent.wifiStaticIp);
  cJSON_AddStringToObject(persistent, "wifiStaticNetmask", g_persistent.wifiStaticNetmask);
  cJSON_AddStringToObject(persistent, "wifiStaticGateway", g_persistent.wifiStaticGateway);
  cJSON_AddStringToObject(persistent, "wifiStaticDns", g_persistent.wifiStaticDns);

  cJSON_AddNumberToObject(persistent, "webPort", g_persistent.webPort);
  cJSON_AddStringToObject(persistent, "webUser", g_persistent.webUser);
  backup_add_encrypted_str_field(persistent, "webPassword", g_persistent.webPassword);

  cJSON_AddNumberToObject(persistent, "enableVscpLink", g_persistent.enableVscpLink);
  cJSON_AddNumberToObject(persistent, "vscplinkPort", g_persistent.vscplinkPort);
  cJSON_AddStringToObject(persistent, "vscplinkUser", g_persistent.vscplinkUser);
  backup_add_encrypted_str_field(persistent, "vscplinkPw", g_persistent.vscplinkPw);

  cJSON_AddNumberToObject(persistent, "enableMqtt", g_persistent.enableMqtt);
  cJSON_AddNumberToObject(persistent, "enableMqttTls", g_persistent.enableMqttTls);
  cJSON_AddStringToObject(persistent, "mqttUrl", g_persistent.mqttUrl);
  cJSON_AddNumberToObject(persistent, "mqttPort", g_persistent.mqttPort);
  cJSON_AddStringToObject(persistent, "mqttUser", g_persistent.mqttUser);
  backup_add_encrypted_str_field(persistent, "mqttPw", g_persistent.mqttPw);
  cJSON_AddStringToObject(persistent, "mqttPubTopic", g_persistent.mqttPubTopic);
  cJSON_AddStringToObject(persistent, "mqttSubTopic", g_persistent.mqttSubTopic);
  cJSON_AddStringToObject(persistent, "mqttPubLogTopic", g_persistent.mqttPubLogTopic);
  cJSON_AddStringToObject(persistent, "mqttClientId", g_persistent.mqttClientId);
  backup_add_encrypted_str_field(persistent, "mqttCaCert", g_persistent.mqttCaCert);
  backup_add_encrypted_str_field(persistent, "mqttClientCert", g_persistent.mqttClientCert);
  backup_add_encrypted_str_field(persistent, "mqttClientKey", g_persistent.mqttClientKey);
  cJSON_AddNumberToObject(persistent, "mqttQos", g_persistent.mqttQos);
  cJSON_AddNumberToObject(persistent, "mqttRetain", g_persistent.mqttRetain);
  cJSON_AddNumberToObject(persistent, "mqttFormat", g_persistent.mqttFormat);

  cJSON_AddNumberToObject(persistent, "enableMulticast", g_persistent.enableMulticast);
  cJSON_AddStringToObject(persistent, "multicastUrl", g_persistent.multicastUrl);
  cJSON_AddNumberToObject(persistent, "multicastPort", g_persistent.multicastPort);
  cJSON_AddNumberToObject(persistent, "multicastTtl", g_persistent.multicastTtl);
  cJSON_AddNumberToObject(persistent, "bMcastEncrypt", g_persistent.bMcastEncrypt);
  cJSON_AddNumberToObject(persistent, "bHeartbeat", g_persistent.bHeartbeat);

  cJSON_AddNumberToObject(persistent, "enableUdpRx", g_persistent.enableUdpRx);
  cJSON_AddNumberToObject(persistent, "enableUdpTx", g_persistent.enableUdpTx);
  cJSON_AddStringToObject(persistent, "udpUrl", g_persistent.udpUrl);
  cJSON_AddNumberToObject(persistent, "udpPort", g_persistent.udpPort);
  cJSON_AddNumberToObject(persistent, "bUdpEncrypt", g_persistent.bUdpEncrypt);

  cJSON_AddNumberToObject(persistent, "enableWebsock", g_persistent.enableWebsock);
  cJSON_AddNumberToObject(persistent, "websockPort", g_persistent.websockPort);
  cJSON_AddStringToObject(persistent, "websockUser", g_persistent.websockUser);
  backup_add_encrypted_str_field(persistent, "websockPw", g_persistent.websockPw);

  char *json = cJSON_Print(root);
  cJSON_Delete(root);

  if (NULL == json) {
    httpd_resp_send_err(req, HTTPD_500_INTERNAL_SERVER_ERROR, "Unable to serialize backup JSON");
    return ESP_FAIL;
  }

  httpd_resp_set_type(req, "application/json");
  httpd_resp_set_hdr(req, "Content-Disposition", "attachment; filename=\"vscp-persistent-backup.json\"");
  httpd_resp_set_hdr(req, "Cache-Control", "no-store");
  esp_err_t rv = httpd_resp_send(req, json, HTTPD_RESP_USE_STRLEN);

  cJSON_free(json);
  return rv;
}

///////////////////////////////////////////////////////////////////////////////
// backup_parse_hex_field
//

static bool
backup_parse_hex_field(const char *str, uint8_t *out, size_t out_len)
{
  if ((NULL == str) || (NULL == out) || (0 == out_len)) {
    return false;
  }

  size_t hex_count = 0;
  for (size_t i = 0; str[i] != '\0'; i++) {
    if (isxdigit((unsigned char) str[i])) {
      hex_count++;
    }
  }

  if (hex_count != (out_len * 2)) {
    return false;
  }

  size_t idx = 0;
  int hi     = -1;
  for (size_t i = 0; str[i] != '\0'; i++) {
    if (!isxdigit((unsigned char) str[i])) {
      continue;
    }

    int nibble = 0;
    if ((str[i] >= '0') && (str[i] <= '9')) {
      nibble = str[i] - '0';
    }
    else if ((str[i] >= 'a') && (str[i] <= 'f')) {
      nibble = 10 + (str[i] - 'a');
    }
    else {
      nibble = 10 + (str[i] - 'A');
    }

    if (hi < 0) {
      hi = nibble;
    }
    else {
      if (idx >= out_len) {
        return false;
      }
      out[idx++] = (uint8_t) ((hi << 4) | nibble);
      hi         = -1;
    }
  }

  return (idx == out_len);
}

static void backup_json_get_u8(const cJSON *obj, const char *name, uint8_t *target)
{
  const cJSON *item = cJSON_GetObjectItemCaseSensitive(obj, name);
  if ((NULL != item) && cJSON_IsNumber(item) && (NULL != target)) {
    *target = (uint8_t) item->valueint;
  }
}

static void backup_json_get_u16(const cJSON *obj, const char *name, uint16_t *target)
{
  const cJSON *item = cJSON_GetObjectItemCaseSensitive(obj, name);
  if ((NULL != item) && cJSON_IsNumber(item) && (NULL != target)) {
    *target = (uint16_t) item->valueint;
  }
}

static void backup_json_get_u32(const cJSON *obj, const char *name, uint32_t *target)
{
  const cJSON *item = cJSON_GetObjectItemCaseSensitive(obj, name);
  if ((NULL != item) && cJSON_IsNumber(item) && (NULL != target)) {
    *target = (uint32_t) item->valuedouble;
  }
}

static void backup_json_get_str(const cJSON *obj, const char *name, char *target, size_t target_len)
{
  const cJSON *item = cJSON_GetObjectItemCaseSensitive(obj, name);
  if ((NULL != item) && cJSON_IsString(item) && (NULL != item->valuestring) && (NULL != target) && (target_len > 0)) {
    strncpy(target, item->valuestring, target_len - 1);
    target[target_len - 1] = '\0';
  }
}

static void
backup_json_get_secret_str(const cJSON *obj, const char *name, char *target, size_t target_len)
{
  const cJSON *item = cJSON_GetObjectItemCaseSensitive(obj, name);
  if ((NULL == item) || !cJSON_IsString(item) || (NULL == item->valuestring) || (NULL == target) || (target_len < 2)) {
    return;
  }

  size_t written = 0;
  if (backup_decrypt_from_hex(name, item->valuestring, (uint8_t *) target, target_len - 1, &written)) {
    target[written] = '\0';
    return;
  }

  strncpy(target, item->valuestring, target_len - 1);
  target[target_len - 1] = '\0';
}

static void
backup_json_get_secret_blob(const cJSON *obj, const char *name, uint8_t *target, size_t target_len)
{
  const cJSON *item = cJSON_GetObjectItemCaseSensitive(obj, name);
  if ((NULL == item) || !cJSON_IsString(item) || (NULL == item->valuestring) || (NULL == target) || (0 == target_len)) {
    return;
  }

  size_t written = 0;
  if (backup_decrypt_from_hex(name, item->valuestring, target, target_len, &written)) {
    return;
  }

  // Backward compatibility: old backup used plain hex for PMK.
  backup_parse_hex_field(item->valuestring, target, target_len);
}

static esp_err_t save_persistent_to_nvs(void)
{
  esp_err_t rv = ESP_OK;

  rv |= nvs_set_str(g_nvsHandle, "nodeName", g_persistent.nodeName);
  rv |= nvs_set_blob(g_nvsHandle, "guid", g_persistent.guid, sizeof(g_persistent.guid));
  rv |= nvs_set_blob(g_nvsHandle, "pmk", g_persistent.pmk, sizeof(g_persistent.pmk));
  rv |= nvs_set_u8(g_nvsHandle, "encryptLvl", g_persistent.encryptLvl);
  rv |= nvs_set_u8(g_nvsHandle, "zone", g_persistent.nodeZone);
  rv |= nvs_set_u8(g_nvsHandle, "subzone", g_persistent.nodeSubzone);
  rv |= nvs_set_u8(g_nvsHandle, "nodeZone", g_persistent.nodeZone);
  rv |= nvs_set_u8(g_nvsHandle, "nodeSubZone", g_persistent.nodeSubzone);

  rv |= nvs_set_u8(g_nvsHandle, "canMode", g_persistent.canMode);
  rv |= nvs_set_u8(g_nvsHandle, "canSpeed", g_persistent.canSpeed);
  rv |= nvs_set_u32(g_nvsHandle, "canFilter", g_persistent.canFilter);
  rv |= nvs_set_u32(g_nvsHandle, "filter", g_persistent.canFilter);
  rv |= nvs_set_u8(g_nvsHandle, "canRaw", g_persistent.bRawCan);

  rv |= nvs_set_u8(g_nvsHandle, "logType", g_persistent.logType);
  rv |= nvs_set_u8(g_nvsHandle, "logRetries", g_persistent.logRetries);
  rv |= nvs_set_u8(g_nvsHandle, "logLevel", g_persistent.logLevel);
  rv |= nvs_set_u8(g_nvsHandle, "log_level", g_persistent.logLevel);
  rv |= nvs_set_u16(g_nvsHandle, "logPort", g_persistent.logPort);
  rv |= nvs_set_str(g_nvsHandle, "logUrl", g_persistent.logUrl);
  rv |= nvs_set_str(g_nvsHandle, "log_url", g_persistent.logUrl);
  rv |= nvs_set_str(g_nvsHandle, "logMqttTopic", g_persistent.logMqttTopic);
  rv |= nvs_set_u8(g_nvsHandle, "enableMqttLog", g_persistent.enableMqttLog);

  rv |= nvs_set_str(g_nvsHandle, "wifiPriSsid", g_persistent.wifiPrimarySsid);
  rv |= nvs_set_str(g_nvsHandle, "wifiPriPass", g_persistent.wifiPrimaryPassword);
  rv |= nvs_set_str(g_nvsHandle, "wifiSecSsid", g_persistent.wifiSecondarySsid);
  rv |= nvs_set_str(g_nvsHandle, "wifiSecPass", g_persistent.wifiSecondaryPassword);
  rv |= nvs_set_u8(g_nvsHandle, "wifiStaIpEn", g_persistent.wifiStaticEnable);
  rv |= nvs_set_str(g_nvsHandle, "wifiStaIp", g_persistent.wifiStaticIp);
  rv |= nvs_set_str(g_nvsHandle, "wifiStaMask", g_persistent.wifiStaticNetmask);
  rv |= nvs_set_str(g_nvsHandle, "wifiStaGw", g_persistent.wifiStaticGateway);
  rv |= nvs_set_str(g_nvsHandle, "wifiStaDns", g_persistent.wifiStaticDns);

  rv |= nvs_set_u16(g_nvsHandle, "webPort", g_persistent.webPort);
  rv |= nvs_set_str(g_nvsHandle, "webUser", g_persistent.webUser);
  rv |= nvs_set_str(g_nvsHandle, "webPassword", g_persistent.webPassword);

  rv |= nvs_set_u8(g_nvsHandle, "enableVscpLink", g_persistent.enableVscpLink);
  rv |= nvs_set_u16(g_nvsHandle, "vscplinkPort", g_persistent.vscplinkPort);
  rv |= nvs_set_str(g_nvsHandle, "vscplinkUser", g_persistent.vscplinkUser);
  rv |= nvs_set_str(g_nvsHandle, "vscplinkPw", g_persistent.vscplinkPw);

  rv |= nvs_set_u8(g_nvsHandle, "enableMqtt", g_persistent.enableMqtt);
  rv |= nvs_set_u8(g_nvsHandle, "enableMqttTls", g_persistent.enableMqttTls);
  rv |= nvs_set_str(g_nvsHandle, "mqttUrl", g_persistent.mqttUrl);
  rv |= nvs_set_u16(g_nvsHandle, "mqttPort", g_persistent.mqttPort);
  rv |= nvs_set_str(g_nvsHandle, "mqttUser", g_persistent.mqttUser);
  rv |= nvs_set_str(g_nvsHandle, "mqttPw", g_persistent.mqttPw);
  rv |= nvs_set_str(g_nvsHandle, "mqttPubTopic", g_persistent.mqttPubTopic);
  rv |= nvs_set_str(g_nvsHandle, "mqttSubTopic", g_persistent.mqttSubTopic);
  rv |= nvs_set_str(g_nvsHandle, "mqttPubLogTopic", g_persistent.mqttPubLogTopic);
  rv |= nvs_set_str(g_nvsHandle, "mqttClientId", g_persistent.mqttClientId);
  rv |= nvs_set_str(g_nvsHandle, "mqttCaCert", g_persistent.mqttCaCert);
  rv |= nvs_set_str(g_nvsHandle, "mqttClientCert", g_persistent.mqttClientCert);
  rv |= nvs_set_str(g_nvsHandle, "mqttClientKey", g_persistent.mqttClientKey);
  rv |= nvs_set_u8(g_nvsHandle, "mqttQos", g_persistent.mqttQos);
  rv |= nvs_set_u8(g_nvsHandle, "mqttRetain", g_persistent.mqttRetain);
  rv |= nvs_set_u8(g_nvsHandle, "mqttFormat", g_persistent.mqttFormat);

  rv |= nvs_set_u8(g_nvsHandle, "enableMulticast", g_persistent.enableMulticast);
  rv |= nvs_set_str(g_nvsHandle, "multicastUrl", g_persistent.multicastUrl);
  rv |= nvs_set_u16(g_nvsHandle, "multicastPort", g_persistent.multicastPort);
  rv |= nvs_set_u8(g_nvsHandle, "multicastTtl", g_persistent.multicastTtl);
  rv |= nvs_set_u8(g_nvsHandle, "bMcastEncrypt", g_persistent.bMcastEncrypt);
  rv |= nvs_set_u8(g_nvsHandle, "bMcastHbeat", g_persistent.bHeartbeat);

  rv |= nvs_set_u8(g_nvsHandle, "enableUdpRx", g_persistent.enableUdpRx);
  rv |= nvs_set_u8(g_nvsHandle, "enableUdpTx", g_persistent.enableUdpTx);
  rv |= nvs_set_str(g_nvsHandle, "udpUrl", g_persistent.udpUrl);
  rv |= nvs_set_u16(g_nvsHandle, "udpPort", g_persistent.udpPort);
  rv |= nvs_set_u8(g_nvsHandle, "bUdpEncrypt", g_persistent.bUdpEncrypt);

  rv |= nvs_set_u8(g_nvsHandle, "enableWebsock", g_persistent.enableWebsock);
  rv |= nvs_set_u16(g_nvsHandle, "websockPort", g_persistent.websockPort);
  rv |= nvs_set_str(g_nvsHandle, "websockUser", g_persistent.websockUser);
  rv |= nvs_set_str(g_nvsHandle, "websockPw", g_persistent.websockPw);

  if (ESP_OK != rv) {
    return rv;
  }

  return nvs_commit(g_nvsHandle);
}

static esp_err_t
config_restore_get_handler(httpd_req_t *req)
{
  char *buf;
  char *req_buf;
  size_t req_buf_len;

  buf = (char *) calloc(CHUNK_BUFSIZE, 1);
  if (NULL == buf) {
    return ESP_ERR_NO_MEM;
  }

  const esp_app_desc_t *appDescr = esp_app_get_description();

  req_buf_len = httpd_req_get_hdr_value_len(req, "Host") + 1;
  if (req_buf_len > 1) {
    req_buf = (char *) malloc(req_buf_len);
    if (httpd_req_get_hdr_value_str(req, "Host", req_buf, req_buf_len) == ESP_OK) {
      ESP_LOGD(TAG, "Found header => Host: %s", req_buf);
    }
    free(req_buf);
  }

  sprintf(buf, WEBPAGE_START_TEMPLATE, g_persistent.nodeName, "Restore Configuration");
  httpd_resp_send_chunk(req, buf, HTTPD_RESP_USE_STRLEN);

  sprintf(buf,
          "<div><form id=restoreForm class=\"button\" onsubmit=\"return false;\"><fieldset>"
          "<label for=\"restorefile\">Backup JSON file:</label>"
          "<input type=\"file\" id=\"restorefile\" accept=\"application/json,.json\" />"
          "<button id=\"restorebtn\" class=\"bgrn\" onclick=\"startRestore()\">Restore and Restart</button>"
          "<p id=\"restorestatus\" class=\"prop\"></p>"
          "</fieldset></form></div>");
  httpd_resp_send_chunk(req, buf, HTTPD_RESP_USE_STRLEN);

  sprintf(buf,
          "<script>"
          "function startRestore(){"
          "var f=document.getElementById('restorefile').files;"
          "var st=document.getElementById('restorestatus');"
          "if(!f||!f.length){alert('Please select a backup JSON file.');return;}"
          "document.getElementById('restorebtn').disabled=true;"
          "st.textContent='Uploading backup...';"
          "var xhr=new XMLHttpRequest();"
          "xhr.onreadystatechange=function(){"
          "if(xhr.readyState===4){"
          "if(xhr.status===200){"
          "document.open();"
          "document.write(xhr.responseText);"
          "document.close();"
          "}else{"
          "st.textContent='Restore failed: '+xhr.status;"
          "document.getElementById('restorebtn').disabled=false;"
          "}"
          "}"
          "};"
          "xhr.open('POST','/docfgrestore',true);"
          "xhr.setRequestHeader('Content-Type','application/json');"
          "xhr.send(f[0]);"
          "}"
          "</script>");
  httpd_resp_send_chunk(req, buf, HTTPD_RESP_USE_STRLEN);

  sprintf(buf, WEBPAGE_CONFIG_END_TEMPLATE, web_ui_version(appDescr), g_persistent.nodeName);
  httpd_resp_send_chunk(req, buf, HTTPD_RESP_USE_STRLEN);
  httpd_resp_send_chunk(req, NULL, 0);
  free(buf);

  return ESP_OK;
}
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
