grodansparadis/vscp-din-wireless-esp32-can-z102/firmware/main/vscp-binary.c

/* ******************************************************************************
 * VSCP (Very Simple Control Protocol)
 * http://www.vscp.org
 *
 * The MIT License (MIT)
 *
 * Copyright (C) 2000-2026 Ake Hedman,
 * The VSCP Project <info@grodansparadis.com>
 *
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
 *  This file is part of VSCP - Very Simple Control Protocol
 *  http://www.vscp.org
 *
 * ******************************************************************************
 */

#include <string.h>
#include <stdlib.h>
#include <stdio.h>
#include <ctype.h>

#include "vscp-compiler.h"
#include "vscp-projdefs.h"

#include <vscp.h>
#include <vscp-firmware-helper.h>

#include "vscp-binary.h"

#define VSCP_ERROR_UNKNOWN_COMMAND 72 /* This command is not available */

///////////////////////////////////////////////////////////////////////////////
// vscp_handle_binary_command
//

int
vscp_handle_binary_command(const void *pdata, uint16_t command, const uint8_t *parg, size_t len)
{
  int rv;

  if (VSCP_BINARY_COMMAND_CODE_NOOP == command) {
    // No operation, just reply with success
    return vscp_binary_callback_reply(pdata, command, VSCP_ERROR_SUCCESS, NULL, 0);
  }
  else if (VSCP_BINARY_COMMAND_CODE_QUIT == command) {
    // Quit command, close connection
    return vscp_binary_callback_quit(pdata);
  }
  else if (VSCP_BINARY_COMMAND_CODE_USER == command) {
    rv = vscp_binary_callback_user(pdata, (const char *) parg);
    return vscp_binary_callback_reply(pdata, command, rv, NULL, 0);
  }
  else if (VSCP_BINARY_COMMAND_CODE_PASS == command) {
    rv = vscp_binary_callback_password(pdata, (const char *) parg);
    vscp_binary_callback_reply(pdata, command, rv, NULL, 0);
  }
  else if (VSCP_BINARY_COMMAND_CODE_CHALLENGE == command) {
    uint8_t challenge[16];
    rv = vscp_binary_callback_challenge(pdata, challenge, sizeof(challenge));
    return vscp_binary_callback_reply(pdata, command, rv, challenge, sizeof(challenge));
  }
  else if (VSCP_BINARY_COMMAND_CODE_SEND == command) {
    vscp_event_t *pev = (vscp_event_t *) calloc(1, sizeof(vscpEvent));
    if (NULL == pev) {
      return vscp_binary_callback_reply(pdata, command, VSCP_ERROR_MEMORY, NULL, 0);
    }

    // Parse event data from parg and fill ex structure
    if (VSCP_ERROR_SUCCESS != (rv = vscp_fwhlp_getEventFromFrame(pev, parg, len))) {
      vscp_fwhlp_deleteEvent(&pev);
      return vscp_binary_callback_reply(pdata, command, rv, NULL, 0);
    }

    int rv = vscp_binary_callback_send_event(pdata, pev);
    vscp_fwhlp_deleteEvent(&pev);

    return vscp_binary_callback_reply(pdata, command, rv, NULL, 0);
  }
  else if (VSCP_BINARY_COMMAND_CODE_RETR == command) {
    uint16_t count = 1; // Default to retrieving one event

    // If the channel is open for asynchronous events then RETR command is not needed and
    // should return VSCP_ERROR_UNSUPPORTED indicating that events will be sent asynchronously.
    if (vscp_binary_callback_is_open(pdata)) {
      return vscp_binary_callback_reply(pdata, command, VSCP_ERROR_UNSUPPORTED, NULL, 0);
    }

    // Check argument length
    if (len >= 2) {
      count = (parg[0] << 8) | parg[1];
    }

    for (int i = 0; i < count; i++) {
      int rv;
      vscp_event_t *pev;
      if (VSCP_ERROR_SUCCESS == (rv = vscp_binary_callback_get_event(pdata, pev))) {

        // Send event data back to client
        size_t buflen = vscp_fwhlp_getFrameSizeFromEvent(pev);

        // Allocate buffer for frame data
        uint8_t *buf = (uint8_t *) malloc(buflen);
        if (NULL == buf) {
          vscp_fwhlp_deleteEvent(&pev);
          return vscp_binary_callback_reply(pdata, command, VSCP_ERROR_MEMORY, NULL, 0);
        }

        // Frame to buffer (this has encodingbyte and crc which we do not need here)
        if (VSCP_ERROR_SUCCESS != (rv = vscp_fwhlp_writeEventToFrame(buf, buflen, 0, pev))) {
          free(buf);
          vscp_fwhlp_deleteEvent(&pev);
          return vscp_binary_callback_reply(pdata, command, rv, NULL, 0);
        }

        // Send reply with event data (point beyond leading byte. That byte + crc is subtracted from lenth)
        if (VSCP_ERROR_SUCCESS !=
            (rv = vscp_binary_callback_reply(pdata, command, VSCP_ERROR_SUCCESS, buf + 1, buflen - 3))) {
          free(buf);
          vscp_fwhlp_deleteEvent(&pev);
          return rv;
        }

        free(buf);
        vscp_fwhlp_deleteEvent(&pev);
      }
      else if (VSCP_ERROR_FIFO_EMPTY == rv) {
        // No more events to retrieve
        break;
      }
      else {
        // Error occurred while retrieving event
        return vscp_binary_callback_reply(pdata, command, rv, NULL, 0);
      }
    } // for

    // All was OK
    return vscp_binary_callback_reply(pdata, command, 0, NULL, 0);
  }
  else if (VSCP_BINARY_COMMAND_CODE_OPEN == command) {
    rv = vscp_binary_callback_open(pdata);
    return vscp_binary_callback_reply(pdata, command, rv, NULL, 0);
  }
  else if (VSCP_BINARY_COMMAND_CODE_CLOSE == command) {
    rv = vscp_binary_callback_close(pdata);
    return vscp_binary_callback_reply(pdata, command, rv, NULL, 0);
  }
  else if (VSCP_BINARY_COMMAND_CODE_CHKDATA == command) {
    uint32_t count;
    if (VSCP_ERROR_SUCCESS != (rv = vscp_binary_callback_check_data(pdata, &count))) {
      return vscp_binary_callback_reply(pdata, command, rv, NULL, 0);
    }
    else {
      uint8_t buf[4];
      buf[0] = (count >> 24) & 0xFF;
      buf[1] = (count >> 16) & 0xFF;
      buf[2] = (count >> 8) & 0xFF;
      buf[3] = count & 0xFF;

      // Send reply with count of events ready to be received
      return vscp_binary_callback_reply(pdata, command, VSCP_ERROR_SUCCESS, buf, sizeof(buf));
    }
  }
  else if (VSCP_BINARY_COMMAND_CODE_CLEAR == command) {
    rv = vscp_binary_callback_clrall(pdata);
    return vscp_binary_callback_reply(pdata, command, rv, NULL, 0);
  }
  else if (VSCP_BINARY_COMMAND_CODE_STAT == command) {
    vscp_statistics_t statistics;
    if (VSCP_ERROR_SUCCESS != (rv = vscp_binary_callback_statistics(pdata, &statistics))) {
      return vscp_binary_callback_reply(pdata, command, rv, NULL, 0);
    }
    else {
      uint8_t buf[28];
      // Fill buf with statistical information from statistics structure
      buf[0] = (statistics.x >> 24) & 0xFF;
      buf[1] = (statistics.x >> 16) & 0xFF;
      buf[2] = (statistics.x >> 8) & 0xFF;
      buf[3] = statistics.x & 0xFF;

      buf[4] = (statistics.y >> 24) & 0xFF;
      buf[5] = (statistics.y >> 16) & 0xFF;
      buf[6] = (statistics.y >> 8) & 0xFF;
      buf[7] = statistics.y & 0xFF;

      buf[8]  = (statistics.z >> 24) & 0xFF;
      buf[9]  = (statistics.z >> 16) & 0xFF;
      buf[10] = (statistics.z >> 8) & 0xFF;
      buf[11] = statistics.z & 0xFF;

      buf[12] = (statistics.cntReceiveData >> 24) & 0xFF;
      buf[13] = (statistics.cntReceiveData >> 16) & 0xFF;
      buf[14] = (statistics.cntReceiveData >> 8) & 0xFF;
      buf[15] = statistics.cntReceiveData & 0xFF;

      buf[16] = (statistics.cntReceiveFrames >> 24) & 0xFF;
      buf[17] = (statistics.cntReceiveFrames >> 16) & 0xFF;
      buf[18] = (statistics.cntReceiveFrames >> 8) & 0xFF;
      buf[19] = statistics.cntReceiveFrames & 0xFF;

      buf[20] = (statistics.cntTransmitData >> 24) & 0xFF;
      buf[21] = (statistics.cntTransmitData >> 16) & 0xFF;
      buf[22] = (statistics.cntTransmitData >> 8) & 0xFF;
      buf[23] = statistics.cntTransmitData & 0xFF;

      buf[24] = (statistics.cntTransmitFrames >> 24) & 0xFF;
      buf[25] = (statistics.cntTransmitFrames >> 16) & 0xFF;
      buf[26] = (statistics.cntTransmitFrames >> 8) & 0xFF;
      buf[27] = statistics.cntTransmitFrames & 0xFF;

      // Send reply with statistical information
      return vscp_binary_callback_reply(pdata, command, VSCP_ERROR_SUCCESS, buf, sizeof(buf));
    }
  }
  else if (VSCP_BINARY_COMMAND_CODE_INFO == command) {
    vscp_status_t status;
    if (VSCP_ERROR_SUCCESS != (rv = vscp_binary_callback_info(pdata, &status))) {
      return vscp_binary_callback_reply(pdata, command, rv, NULL, 0);
    }
    else {
      uint8_t buf[12];
      // Fill buf with status information from status structure
      buf[0] = (status.channel_status >> 24) & 0xFF;
      buf[1] = (status.channel_status >> 16) & 0xFF;
      buf[2] = (status.channel_status >> 8) & 0xFF;
      buf[3] = status.channel_status & 0xFF;

      buf[4] = (status.lasterrorcode >> 24) & 0xFF;
      buf[5] = (status.lasterrorcode >> 16) & 0xFF;
      buf[6] = (status.lasterrorcode >> 8) & 0xFF;
      buf[7] = status.lasterrorcode & 0xFF;

      buf[8]  = (status.lasterrorsubcode >> 24) & 0xFF;
      buf[9]  = (status.lasterrorsubcode >> 16) & 0xFF;
      buf[10] = (status.lasterrorsubcode >> 8) & 0xFF;
      buf[11] = status.lasterrorsubcode & 0xFF;

      // Send reply with status information
      return vscp_binary_callback_reply(pdata, command, VSCP_ERROR_SUCCESS, buf, sizeof(buf));
    }
  }
  else if (VSCP_BINARY_COMMAND_CODE_GETCHID == command) {
    uint32_t chid;
    rv = vscp_binary_callback_get_chid(pdata, &chid);
    if (VSCP_ERROR_SUCCESS != rv) {
      return vscp_binary_callback_reply(pdata, command, rv, NULL, 0);
    }
    else {
      // Send reply with channel id
      uint8_t buf[4];
      buf[0] = (chid >> 24) & 0xFF;
      buf[1] = (chid >> 16) & 0xFF;
      buf[2] = (chid >> 8) & 0xFF;
      buf[3] = chid & 0xFF;
      return vscp_binary_callback_reply(pdata, command, rv, buf, sizeof(buf));
    }
  }
  else if (VSCP_BINARY_COMMAND_CODE_SETGUID == command) {
    uint8_t guid[16];
    if (VSCP_ERROR_SUCCESS != (rv = vscp_binary_callback_set_guid(pdata, guid))) {
      return rv;
    }
    // Send reply with GUID
    return vscp_binary_callback_reply(pdata, command, VSCP_ERROR_SUCCESS, NULL, 0);
  }
  else if (VSCP_BINARY_COMMAND_CODE_GETGUID == command) {
    uint8_t guid[16];
    if (VSCP_ERROR_SUCCESS != (rv = vscp_binary_callback_get_guid(pdata, guid))) {
      return vscp_binary_callback_reply(pdata, command, rv, NULL, 0);
    }
    // Send reply with GUID
    return vscp_binary_callback_reply(pdata, command, VSCP_ERROR_SUCCESS, guid, 16);
  }
  else if (VSCP_BINARY_COMMAND_CODE_VERSION == command) {
    uint8_t version[10]; // 2 + 2 + 2 + 4
    if (VSCP_ERROR_SUCCESS != (rv = vscp_binary_callback_get_version(pdata, version))) {
      return vscp_binary_callback_reply(pdata, command, rv, version, sizeof(version));
    }
    // Send reply with version
    return vscp_binary_callback_reply(pdata, command, VSCP_ERROR_SUCCESS, version, sizeof(version));
  }
  else if (VSCP_BINARY_COMMAND_CODE_SETFILTER == command) {
    vscpEventFilter filter;

    /*
      len can be 21 or 42 as it is possible to send filter AND mask in the same command
    */
    if (len < 21) {
      return vscp_binary_callback_reply(pdata, command, VSCP_ERROR_PARAMETER, NULL, 0);
    }

    // read filter part of argument
    filter.filter_priority = parg[0];
    filter.filter_class    = (parg[1] << 8) | parg[2];
    filter.filter_type     = (parg[3] << 8) | parg[4];
    memcpy(filter.filter_GUID, parg + 5, 16);

    if (VSCP_ERROR_SUCCESS != (rv = vscp_binary_callback_setfilter(pdata, &filter))) {
      return vscp_binary_callback_reply(pdata, command, rv, NULL, 0);
    }

    if (len >= 42) {
      // read mask part of argument if present (mask part is ignored by callback but can be used by client to keep track
      // of mask)
      filter.mask_priority = parg[21];
      filter.mask_class    = (parg[22] << 8) | parg[23];
      filter.mask_type     = (parg[24] << 8) | parg[25];
      memcpy(filter.mask_GUID, parg + 26, 16);

      if (VSCP_ERROR_SUCCESS != (rv = vscp_binary_callback_setmask(pdata, &filter))) {
        return vscp_binary_callback_reply(pdata, command, rv, NULL, 0);
      }
    }

    return vscp_binary_callback_reply(pdata, command, VSCP_ERROR_SUCCESS, NULL, 0);
  }
  else if (VSCP_BINARY_COMMAND_CODE_SETMASK == command) {
    vscpEventFilter filter;
    if (len < 21) {
      return vscp_binary_callback_reply(pdata, command, VSCP_ERROR_PARAMETER, NULL, 0);
    }

    // read mask part of argument
    filter.mask_priority = parg[0];
    filter.mask_class    = (parg[1] << 8) | parg[2];
    filter.mask_type     = (parg[3] << 8) | parg[4];
    memcpy(filter.mask_GUID, parg + 5, 16);

    if (VSCP_ERROR_SUCCESS != (rv = vscp_binary_callback_setmask(pdata, &filter))) {
      return vscp_binary_callback_reply(pdata, command, rv, NULL, 0);
    }

    return vscp_binary_callback_reply(pdata, command, VSCP_ERROR_SUCCESS, NULL, 0);
  }
  else if (VSCP_BINARY_COMMAND_CODE_INTERFACE == command) {
    /*!
      Argument = 0 - Get interface count
      Argument = 1 - Get interface information interface. (index as second argument)
      Argument = 2 - Close interface (index as second argument)
      Argument = 3 - Open interface (index as second argument)
    */

    if (len == 1 && parg[0] == 0) {
      // Get interface count
      uint16_t count;
      if (VSCP_ERROR_SUCCESS != (rv = vscp_binary_callback_get_interface_count(pdata, &count))) {
        return vscp_binary_callback_reply(pdata, command, rv, NULL, 0);
      }
      // Send reply with count
      uint8_t buf[2];
      buf[0] = (count >> 8) & 0xFF;
      buf[1] = count & 0xFF;
      return vscp_binary_callback_reply(pdata, command, VSCP_ERROR_SUCCESS, buf, sizeof(buf));
    }
    else if (len >= 3 && parg[0] == 1) {
      // Get interface information
      vscp_interface_info_t ifinfo;

      // Interface index
      uint16_t idx = (parg[1] << 8) | parg[2];

      if (VSCP_ERROR_SUCCESS != (rv = vscp_binary_callback_get_interface(pdata, idx, &ifinfo))) {
        return vscp_binary_callback_reply(pdata, command, rv, NULL, 0);
      }

      uint8_t buf[2 + 2 + 16 + 64] = { 0 };
      buf[0]                       = (ifinfo.idx >> 8) & 0xFF;
      buf[1]                       = ifinfo.idx & 0xFF;
      buf[2]                       = (ifinfo.idx >> 8) & 0xFF;
      buf[3]                       = ifinfo.idx & 0xFF;
      memcpy(buf + 4, ifinfo.guid, 16);
      memcpy(buf + 20, ifinfo.description, 64); // Interface description
      return vscp_binary_callback_reply(pdata, command, VSCP_ERROR_SUCCESS, buf, sizeof(buf));
    }
    else if (len >= 3 && parg[0] == 2) {
      // Close interface

      // Interface index
      uint16_t idx = (parg[1] << 8) | parg[2];

      if (VSCP_ERROR_SUCCESS != (rv = vscp_binary_callback_interface_close(pdata, idx))) {
        return vscp_binary_callback_reply(pdata, command, rv, NULL, 0);
      }
      // Send reply confirming interface was closed
      return vscp_binary_callback_reply(pdata, command, VSCP_ERROR_SUCCESS, NULL, 0);
    }
    else if (len >= 3 && parg[0] == 3) {
      // Open interface

      // Interface index
      uint16_t idx = (parg[1] << 8) | parg[2];

      if (VSCP_ERROR_SUCCESS != (rv = vscp_binary_callback_interface_open(pdata, idx))) {
        return vscp_binary_callback_reply(pdata, command, rv, NULL, 0);
      }
      // Send reply confirming interface was opened    return vscp_binary_callback_reply(pdata, command,
      // VSCP_ERROR_SUCCESS, NULL, 0);
      return vscp_binary_callback_reply(pdata, command, VSCP_ERROR_SUCCESS, NULL, 0);
    }

    return vscp_binary_callback_reply(pdata, command, VSCP_ERROR_PARAMETER, NULL, 0);
  }
  else if (VSCP_BINARY_COMMAND_CODE_TEST == command) {
    return vscp_binary_callback_test(pdata, parg, len);
  }
  else if (VSCP_BINARY_COMMAND_CODE_TEXT == command) {
    // We normally do nothing here except resetting binary flag
    rv = vscp_binary_callback_text(pdata);
    return vscp_binary_callback_reply(pdata, command, rv, NULL, 0);
  }
  else if (VSCP_BINARY_COMMAND_CODE_WCYD == command) {
    uint64_t capabilities = 0;
    if (VSCP_ERROR_SUCCESS != (rv = vscp_binary_callback_wcyd(pdata, &capabilities))) {
      return vscp_binary_callback_reply(pdata, command, rv, NULL, 0);
    }
    // Send reply with capabilities
    uint8_t buf[8];
    for (int i = 0; i < 8; i++) {
      buf[i] = (capabilities >> (56 - i * 8)) & 0xFF;
    }
    return vscp_binary_callback_reply(pdata, command, VSCP_ERROR_SUCCESS, buf, sizeof(buf));
  }
  else if (VSCP_BINARY_COMMAND_CODE_SHUTDOWN == command) {
    // Reply and optional shutdown are handled inside the callback
    return vscp_binary_callback_shutdown(pdata);
  }
  else if (VSCP_BINARY_COMMAND_CODE_RESTART == command) {
    // Reply is sent inside the callback before esp_restart() is called
    return vscp_binary_callback_restart(pdata);
  }
  else if (command >= VSCP_BINARY_COMMAND_CODE_USER_START) {
    // User defined command, pass to callback
    return vscp_binary_callback_user_command(pdata, command, parg, len);
  }
  else {
    // Unknown command
    return VSCP_ERROR_UNKNOWN_COMMAND;
  }

  return VSCP_ERROR_SUCCESS;
}

///////////////////////////////////////////////////////////////////////////////
// vscp_handle_binary_event
//

int
vscp_handle_binary_event(const void *pdata, vscp_event_t *pEvent)
{
  int rv;

  if (NULL == pEvent) {
    return VSCP_ERROR_PARAMETER;
  }

  rv = vscp_binary_callback_send_event(pdata, pEvent);

  // Event is deleted in caller routine

  // Fill the reply buffer with data
  uint8_t buf[4] = { 0 };
  buf[0]         = (pEvent->head >> 8) & 0xFF;
  buf[1]         = pEvent->head & 0xFF;
  buf[2]         = (pEvent->crc >> 8) & 0xFF;
  buf[3]         = pEvent->crc & 0xFF;

  return vscp_binary_callback_reply(pdata, VSCP_BINARY_COMMAND_CODE_EVENT_CONFIRM, rv, buf, sizeof(buf));
}
