grodansparadis/vscp-din-wireless-esp32-can-z102/firmware/main/can4vscp.h

/*
 * This file is part of the VSCP CAN4VSCP Gateway project.
 *
 * Copyright (C) 2022  Meatpi Electronics.
 * Original written by Ali Slim <ali@meatpi.com>
 * Changes Copyright (C) 2022-2026 Ake Hedman, the VSCP Project <ake@vscp.org>
 *
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
 https://docs.espressif.com/projects/esp-idf/en/v5.5.2/esp32/api-reference/peripherals/twai.html
 
 
 */


#ifndef __CAN4VSCP_H__
#define __CAN4VSCP_H__

#include <stdbool.h>
#include <stdint.h>

#include <esp_err.h>

#include <freertos/FreeRTOS.h>

// Project-owned CAN frame abstraction.
// Keep field names aligned with legacy TWAI usage to minimize call-site changes.
typedef struct {
  uint32_t identifier;
  uint8_t data_length_code;
  uint8_t data[8];
  uint8_t extd;
  uint8_t rtr;
  uint8_t ss;
  uint8_t self;
  uint8_t dlc_non_comp;
} can4vscp_frame_t;

#define CAN4VSCP_5K				        0   /**< TWAI bus-speed 5K */
#define CAN4VSCP_10K				      1   /**< TWAI bus-speed 10K */
#define CAN4VSCP_20K				      2   /**< TWAI bus-speed 20K */
#define CAN4VSCP_25K				      3   /**< TWAI bus-speed 25K */
#define CAN4VSCP_50K				      4   /**< TWAI bus-speed 50K */
#define CAN4VSCP_100K			        5   /**< TWAI bus-speed 100K */
#define CAN4VSCP_125K			        6   /**< TWAI bus-speed 125K CAN4VSCP speed */
#define CAN4VSCP_250K			        7   /**< TWAI bus-speed 250K */
#define CAN4VSCP_500K			        8   /**< TWAI bus-speed 500K */
#define CAN4VSCP_800K			        9   /**< TWAI bus-speed 800K */
#define CAN4VSCP_1000K			     10   /**< TWAI bus-speed 1M */
#define CAN4VSCP_AUTO            99   /**< TWAI autodetect speed */

/**!
 * @brief TWAI bus speed structure
 */
typedef struct {
	uint8_t bus_state;    /**< State of the bus */
	uint8_t silent;       /**< Silent mode */
	uint8_t loopback;     /**< Loopback mode */
	uint16_t brp;         /**< Bitrate */
	uint8_t phase_seg1;   /**< Phase segment 1 */
	uint8_t phase_seg2;   /**< Phase segment 2 */
	uint8_t sjw;          /**< SJW */
	uint32_t filter;      /**< Message filter */
	uint32_t mask;        /**< Message mask */
} can4vscp_cfg_t;       


/*!
  * @brief Translate CAN4VSCP messge to VSCP event
  * @param pev Pointer to pointer to event that will be allocated and filled with data from message
  * @param msg Pointer to CAN message to translate
  * @return VSCP_ERROR_SUCCESS if all is OK else error code.
  * 
  * The calling function is responsible for freeing the allocated event and its data. 
  * free(*pev->pdata); free(*pev);
  * Data is allocated and filled if the message has data.
  * The event is then filtered using the level 2 filter, and if it passes, it is returned to the caller.
  * If the message is filtered out, the allocated event is freed and VSCP_ERROR_SUCCESS is returned.
*/
int
can4vscp_msg_to_event(vscp_event_t **pev, const can4vscp_frame_t *msg);

/*!
  * @brief Translate VSCP event to CAN4VSCP message
  * @param msg Pointer to CAN message that will be filled with data from event
  * @param pev Pointer to event to translate
  * @return VSCP_ERROR_SUCCESS if all is OK else error code.
  * 
  * The calling function is responsible for freeing the allocated event and its data. 
  * free(*pev->pdata); free(*pev);
  * Data is allocated and filled if the message has data.
*/
int
can4vscp_event_to_msg(can4vscp_frame_t *msg, const vscp_event_t *pev);

/*!
  @fn can4vscp_block
  @brief Block transmission/reception
*/
void
can4vscp_block(void);

/*!
  @fn can4vscp_unblock
  @brief Unblock transmission/reception
*/
void
can4vscp_unblock(void);

/*!
  @fn can4vscp_enable
  @brief Enable TWAI
  Filtering is set so all TWAI messages are received.
*/
void can4vscp_enable(void);

/*!
  @fn can4vscp_disable
  @brief Disable TWAI  
*/
void can4vscp_disable(void);

/*!
  @fn can4vscp_setSilent
  @brief Handle silent mode
  I/f must be disabled to set/reset silent mode
  @param flag Set to 1 for silent, 0 for active.
*/
void can4vscp_setSilent(uint8_t flag);

/*!
  @fn can4vscp_isSilent
  @brief Check if CAN i/f is silent
  @return true if enabled
*/
uint8_t can4vscp_isSilent(void);

/*!
  @fn can4vscp_setLoopback
  @brief Handle loopback mode
  I/f must be disabled to set/reset silent mode
  @param flag Set to 1 for loopback, 0 for normal mode.
*/
void can4vscp_setLoopback(uint8_t flag);

/*!
  @fn can4vscp_isLoopback
  @brief Check if CAN i/f is in loopback mode
  @return true if enabled
*/
uint8_t can4vscp_isLoopback(void);

/*!
  @fn can4vscp_setFilter
  @brief Set filter
  I/f must be disabled to set filter.
  @param filter 32-bit filter value to set
*/
void can4vscp_setFilter(uint32_t filter);

/*!
  @fn can4vscp_setMask
  @brief Set mask
  I/f must be disabled to set mask.
  @param mask 32-bit mask value to set
*/
void can4vscp_setMask(uint32_t mask);

/*!
  @fn can4vscp_setBitrate
  @brief Set bitrate for TWAI bus
  I/f must be disabled to set bitrate.
  @param rate Code for bitrate
*/
void can4vscp_setBitrate(uint8_t rate);

/*!
  @fn can4vscp_getBitrate
  @brief Get bitrate for TWAI bus
  @return Code for set bitrate
*/
uint8_t can4vscp_getBitrate(void);

/*!
  @fn can4vscp_init
  @brief Initialize the TWAI interface
  @param bitrate to use
*/
void can4vscp_init(uint8_t bitrate);

/*!
  @fn can4vscp_receive
  @brief Receive TWAI message w/ auto bauderate
  
  @param message Pointer to message that will get receive data
  @param ticks_to_wait Timeout 
  @return ESP_OK if all is OK else error code.
*/
esp_err_t can4vscp_receive(can4vscp_frame_t *message, TickType_t ticks_to_wait);

/*!
  @fn can4vscp_send
  @brief Send TWAI message
  
  @param message Pointer to message that will be sent
  @param ticks_to_wait Timeout 
  @return ESP_OK if all is OK else error code.
*/
esp_err_t can4vscp_send(can4vscp_frame_t *message, TickType_t ticks_to_wait);

/*!
  @fn can4vscp_isEnabled
  @brief Check if CAN is enabled
  @return true if enabled
*/
bool can4vscp_isEnabled(void);

/*!
  @fn can4vscp_get_bitrate
  @brief Get Bitrate
  @return Code for set bitrate
*/
uint8_t can4vscp_get_bitrate(void);

/*!
  @fn can4vscp_getRxMsgCount
  @brief Get receive message queue count

  @return Receive Queue count
*/
uint32_t can4vscp_getRxMsgCount(void);



// ----------------------------------------------------------------------------
//                                     Tasks
// ----------------------------------------------------------------------------



/*!
  Task that handle receive of messages and fills the 
  rx buffers for different transports. The message broker 
  task is informed about the received message so it is sent 
  to all other tasks
  @param arg CAN4VSCP context
*/
void twai_receive_task(void *arg);

/*!
  Task that handle trasmit of messages from the
  CAN4VSCP tx buffer.
  @param arg CAN4VSCP context
*/
void twai_transmit_task(void *arg);

/*!
  @fn twai_recover_stopped_check
  @brief Check if TWAI is stopped and recover if so
  @param arg Not used
*/
void
twai_recover_stopped_check(void);

#endif
