grodansparadis/vscp-din-wireless-esp32-can-z102/firmware/main/websocksrv.c

/*
  File: websocksrv.h

  VSCP Wireless CAN4VSCP Gateway (VSCP-WCANG)

  This file is part of the VSCP (https://www.vscp.org)

  The MIT License (MIT)
  Copyright (C) 2025-2026 Ake Hedman, the VSCP project <info@vscp.org>

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
  THE SOFTWARE IS PROVIDED "AS IS", WITHOUT WARRANTY OF ANY KIND, EXPRESS OR
  IMPLIED, INCLUDING BUT NOT LIMITED TO THE WARRANTIES OF MERCHANTABILITY,
  FITNESS FOR A PARTICULAR PURPOSE AND NONINFRINGEMENT. IN NO EVENT SHALL THE
  AUTHORS OR COPYRIGHT HOLDERS BE LIABLE FOR ANY CLAIM, DAMAGES OR OTHER
  LIABILITY, WHETHER IN AN ACTION OF CONTRACT, TORT OR OTHERWISE, ARISING FROM,
  OUT OF OR IN CONNECTION WITH THE SOFTWARE OR THE USE OR OTHER DEALINGS IN THE
  SOFTWARE.
*/

#include <stdio.h>
#include <string.h>
#include <ctype.h>
#include <sys/param.h>
#include <sys/unistd.h>
#include <sys/stat.h>
#include <dirent.h>

#include <esp_system.h>
#include <esp_chip_info.h>
#include <esp_flash_spi_init.h>
#include <esp_flash.h>
#include <esp_wifi.h>
#include <esp_mac.h>
#include <nvs.h>
#include <esp_ota_ops.h>
#include <esp_timer.h>
#include <esp_err.h>
#include <esp_log.h>
#include <nvs_flash.h>

#include <esp_event_base.h>
#include <esp_tls_crypto.h>
#include <esp_vfs.h>
#include <esp_spiffs.h>
#include <esp_http_server.h>
// #include <wifi_provisioning/manager.h>
#include "keep-alive.h"
#include "sdkconfig.h"

#include "freertos/FreeRTOS.h"
#include "freertos/task.h"
#include "freertos/event_groups.h"

#include <vscp.h>
#include <vscp-firmware-helper.h>

#include "urldecode.h"
#include "main.h"

#include "vscp-ws-common.h"
#include "vscp-ws1.h"
#include "vscp-ws2.h"
#include "websocksrv.h"

#if !CONFIG_HTTPD_WS_SUPPORT
#error This code cannot be used unless HTTPD_WS_SUPPORT is enabled in esp-http-server component configuration
#endif

// External from main
extern nvs_handle_t g_nvsHandle;
extern node_persistent_config_t g_persistent;
extern vprintf_like_t g_stdLogFunc;

extern transport_t tr_websockets;

#define TAG __func__

static const size_t max_clients = 4;

// Global server handle for WebSocket server instance
httpd_handle_t g_websocket_srv = NULL;
// httpd_handle_t g_server_websocket = NULL;

esp_err_t
wss_close_client_fd(int fd)
{
  if (NULL == g_websocket_srv) {
    ESP_LOGW(TAG, "wss_close_client_fd: websocket server not running");
    return ESP_ERR_INVALID_STATE;
  }

  if (fd < 0) {
    ESP_LOGW(TAG, "wss_close_client_fd: invalid socket fd=%d", fd);
    return ESP_ERR_INVALID_ARG;
  }

  int client_info = httpd_ws_get_fd_info(g_websocket_srv, fd);
  if (HTTPD_WS_CLIENT_WEBSOCKET != client_info) {
    ESP_LOGW(TAG, "wss_close_client_fd: fd=%d is not an active websocket client (info=%d)", fd, client_info);
    return ESP_ERR_NOT_FOUND;
  }

  ESP_LOGI(TAG, "wss_close_client_fd: closing websocket fd=%d", fd);
  return httpd_sess_trigger_close(g_websocket_srv, fd);
}

/*
 * Structure holding server handle
 * and internal socket fd in order
 * to use out of request send
 */
struct async_resp_arg {
  httpd_handle_t hd;
  int fd;
  vscp_event_ex_t ex; // Canonical event payload. Serialization is done in send_event.
};

///////////////////////////////////////////////////////////////////////////////
// ws_async_send
//

static void
ws_async_send(void *arg)
{
  httpd_ws_frame_t ws_pkt;
  struct async_resp_arg *resp_arg = arg;
  httpd_handle_t hd               = resp_arg->hd;

  static int led_state = 0;
  char buf[4];
  memset(buf, 0, sizeof(buf));
  sprintf(buf, "%d", led_state);

  memset(&ws_pkt, 0, sizeof(httpd_ws_frame_t));
  ws_pkt.payload = (uint8_t *) buf;
  ws_pkt.len     = strlen(buf);
  ws_pkt.type    = HTTPD_WS_TYPE_TEXT;

  static size_t max_clients = CONFIG_LWIP_MAX_LISTENING_TCP;
  size_t fds                = max_clients;
  int client_fds[max_clients];

  esp_err_t ret = httpd_get_client_list(g_websocket_srv, &fds, client_fds);

  if (ret != ESP_OK) {
    free(resp_arg);
    return;
  }

  for (int i = 0; i < fds; i++) {
    int client_info = httpd_ws_get_fd_info(g_websocket_srv, client_fds[i]);
    if (client_info == HTTPD_WS_CLIENT_WEBSOCKET) {
      httpd_ws_send_frame_async(hd, client_fds[i], &ws_pkt);
    }
  }
  free(resp_arg);
}

///////////////////////////////////////////////////////////////////////////////
// trigger_async_send
//

static esp_err_t __attribute__((unused))
trigger_async_send(httpd_handle_t handle, httpd_req_t *req)
{
  struct async_resp_arg *resp_arg = malloc(sizeof(struct async_resp_arg));
  if (resp_arg == NULL) {
    return ESP_ERR_NO_MEM;
  }
  resp_arg->hd  = req->handle;
  resp_arg->fd  = httpd_req_to_sockfd(req);
  esp_err_t ret = httpd_queue_work(handle, ws_async_send, resp_arg);
  if (ret != ESP_OK) {
    free(resp_arg);
  }
  return ret;
}

// ----------------------------------------------------------------------------

///////////////////////////////////////////////////////////////////////////////
// wss_open_fd
//

// static esp_err_t
// ws_handler(httpd_req_t *req)
// {
//   if (req->method == HTTP_GET) {
//     ESP_LOGI(TAG, "Handshake done, the new connection was opened");
//     return ESP_OK;
//   }
//   httpd_ws_frame_t ws_pkt;
//   uint8_t *buf = NULL;
//   memset(&ws_pkt, 0, sizeof(httpd_ws_frame_t));

//   // First receive the full ws message
//   /* Set max_len = 0 to get the frame len */
//   esp_err_t ret = httpd_ws_recv_frame(req, &ws_pkt, 0);
//   if (ret != ESP_OK) {
//     ESP_LOGE(TAG, "httpd_ws_recv_frame failed to get frame len with %d", ret);
//     return ret;
//   }
//   ESP_LOGI(TAG, "frame len is %d", ws_pkt.len);
//   if (ws_pkt.len) {
//     /* ws_pkt.len + 1 is for NULL termination as we are expecting a string */
//     buf = calloc(1, ws_pkt.len + 1);
//     if (buf == NULL) {
//       ESP_LOGE(TAG, "Failed to calloc memory for buf");
//       return ESP_ERR_NO_MEM;
//     }
//     ws_pkt.payload = buf;
//     /* Set max_len = ws_pkt.len to get the frame payload */
//     ret = httpd_ws_recv_frame(req, &ws_pkt, ws_pkt.len);
//     if (ret != ESP_OK) {
//       ESP_LOGE(TAG, "httpd_ws_recv_frame failed with %d", ret);
//       free(buf);
//       return ret;
//     }
//   }
//   // If it was a PONG, update the keep-alive
//   if (ws_pkt.type == HTTPD_WS_TYPE_PONG) {
//     ESP_LOGD(TAG, "Received PONG message");
//     free(buf);
//     return wss_keep_alive_client_is_active(httpd_get_global_user_ctx(req->handle), httpd_req_to_sockfd(req));

//     // If it was a TEXT message, just echo it back
//   }
//   else if (ws_pkt.type == HTTPD_WS_TYPE_TEXT || ws_pkt.type == HTTPD_WS_TYPE_PING ||
//            ws_pkt.type == HTTPD_WS_TYPE_CLOSE) {
//     if (ws_pkt.type == HTTPD_WS_TYPE_TEXT) {
//       ESP_LOGI(TAG, "Received packet with message: %s", ws_pkt.payload);
//     }
//     else if (ws_pkt.type == HTTPD_WS_TYPE_PING) {
//       // Response PONG packet to peer
//       ESP_LOGI(TAG, "Got a WS PING frame, Replying PONG");
//       ws_pkt.type = HTTPD_WS_TYPE_PONG;
//     }
//     else if (ws_pkt.type == HTTPD_WS_TYPE_CLOSE) {
//       // Response CLOSE packet with no payload to peer
//       ws_pkt.len     = 0;
//       ws_pkt.payload = NULL;
//     }
//     ret = httpd_ws_send_frame(req, &ws_pkt);
//     if (ret != ESP_OK) {
//       ESP_LOGE(TAG, "httpd_ws_send_frame failed with %d", ret);
//     }
//     ESP_LOGI(TAG,
//              "ws_handler: httpd_handle_t=%p, sockfd=%d, client_info:%d",
//              req->handle,
//              httpd_req_to_sockfd(req),
//              httpd_ws_get_fd_info(req->handle, httpd_req_to_sockfd(req)));
//     free(buf);
//     return ret;
//   }
//   free(buf);
//   return ESP_OK;
// }

///////////////////////////////////////////////////////////////////////////////
// wss_open_fd
//

esp_err_t
wss_open_fd(httpd_handle_t hd, int sockfd)
{
  ESP_LOGI(TAG, "New client connected %d", sockfd);
  wss_keep_alive_t h = httpd_get_global_user_ctx(hd);
  return wss_keep_alive_add_client(h, sockfd);
}

///////////////////////////////////////////////////////////////////////////////
// wss_close_fd
//

void
wss_close_fd(httpd_handle_t hd, int sockfd)
{
  ESP_LOGI(TAG, "Client disconnected %d", sockfd);
  wss_keep_alive_t h = httpd_get_global_user_ctx(hd);
  wss_keep_alive_remove_client(h, sockfd);
  close(sockfd);
}

///////////////////////////////////////////////////////////////////////////////
// send_event
//

static void
send_event(void *arg)
{
  struct async_resp_arg *resp_arg = arg;
  httpd_handle_t hd               = resp_arg->hd;
  int fd                          = resp_arg->fd;

  // We need to check which protocol the client expects
  vscp_ws_connection_context_t *pctx = (vscp_ws_connection_context_t *) httpd_sess_get_ctx(hd, fd);

  if (pctx == NULL) {
    ESP_LOGW(TAG, "send_event: client context is NULL, skipping send for fd=%d", fd);
    free(resp_arg);
    return;
  }

  ESP_LOGI(TAG,
           "send_event: Sending to fd=%d protocol=%d binary=%d enc=%d",
           fd,
           pctx->protocol,
           pctx->bBinary,
           pctx->encryption & 0x0F);

  // Create a new frame with the event payload
  httpd_ws_frame_t ws_pkt;
  memset(&ws_pkt, 0, sizeof(httpd_ws_frame_t));
  if (pctx->bBinary) {
    uint8_t event_bin[1 + VSCP_BINARY_PACKET_FRAME0_HEADER_LENGTH + 2 + 512] = { 0 };
    uint16_t event_bin_len                                                     = vscp_fwhlp_getFrameSizeFromEventEx(&resp_arg->ex);

    if (event_bin_len > sizeof(event_bin)) {
      ESP_LOGE(TAG, "send_event: binary event frame too large len=%u", event_bin_len);
      free(resp_arg);
      return;
    }

    if (VSCP_ERROR_SUCCESS != vscp_fwhlp_writeEventExToFrame(event_bin, sizeof(event_bin), 0, &resp_arg->ex)) {
      ESP_LOGE(TAG, "send_event: failed to format binary event for fd=%d", fd);
      free(resp_arg);
      return;
    }

    const uint8_t encryption = pctx->encryption & 0x0F;

    if (VSCP_HLO_ENCRYPTION_NONE != encryption) {
      uint8_t plain[1 + VSCP_BINARY_PACKET_FRAME0_HEADER_LENGTH + 2 + 512] = { 0 };
      uint8_t enc[sizeof(plain) + 32]                                      = { 0 };

      if (event_bin_len > sizeof(plain)) {
        ESP_LOGE(TAG, "send_event: binary event frame too large for encryption len=%u", event_bin_len);
        free(resp_arg);
        return;
      }

      memcpy(plain, event_bin, event_bin_len);
      plain[0] = (plain[0] & 0xF0) | encryption;

      size_t enclen = vscp_fwhlp_encryptFrame(enc,
                                              plain,
                                              event_bin_len,
                                              (uint8_t *) vscp_ws1_callback_get_primary_key(pctx),
                                              NULL,
                                              VSCP_ENCRYPTION_FROM_TYPE_BYTE);
      if (0 == enclen) {
        ESP_LOGE(TAG, "send_event: failed to encrypt binary event for fd=%d", fd);
        free(resp_arg);
        return;
      }

      ws_pkt.type    = HTTPD_WS_TYPE_BINARY;
      ws_pkt.payload = enc;
      ws_pkt.len     = enclen;

      esp_err_t ret = httpd_ws_send_frame_async(hd, fd, &ws_pkt);
      if (ret != ESP_OK) {
        ESP_LOGE(TAG, "send_event: encrypted async send failed fd=%d err=%d", fd, ret);
      }

      free(resp_arg);
      return;
    }

    ws_pkt.type    = HTTPD_WS_TYPE_BINARY;
    ws_pkt.payload = event_bin;
    ws_pkt.len     = event_bin_len;
  }
  else {
    char event_str[512] = { 0 };
    if (VSCP_ERROR_SUCCESS != vscp_fwhlp_eventToStringEx(event_str, sizeof(event_str), &resp_arg->ex)) {
      ESP_LOGE(TAG, "send_event: failed to format text event for fd=%d", fd);
      free(resp_arg);
      return;
    }

    ws_pkt.type    = HTTPD_WS_TYPE_TEXT;
    ws_pkt.payload = (uint8_t *) event_str;
    ws_pkt.len     = strlen(event_str);
  }

  // Send the frame - httpd_ws_send_frame_async copies the payload internally
  esp_err_t ret = httpd_ws_send_frame_async(hd, fd, &ws_pkt);

  if (ret != ESP_OK) {
    ESP_LOGE(TAG, "send_event: httpd_ws_send_frame_async failed for fd=%d, error=%d", fd, ret);
  }

  free(resp_arg);
}

///////////////////////////////////////////////////////////////////////////////
// send_ping
//

static void
send_ping(void *arg)
{
  struct async_resp_arg *resp_arg = arg;
  httpd_handle_t hd               = resp_arg->hd;
  int fd                          = resp_arg->fd;
  httpd_ws_frame_t ws_pkt;
  memset(&ws_pkt, 0, sizeof(httpd_ws_frame_t));
  ws_pkt.payload = NULL;
  ws_pkt.len     = 0;
  ws_pkt.type    = HTTPD_WS_TYPE_PING;

  httpd_ws_send_frame_async(hd, fd, &ws_pkt);
  free(resp_arg);
}

///////////////////////////////////////////////////////////////////////////////
// client_not_alive_cb
//

bool
client_not_alive_cb(wss_keep_alive_t h, int fd)
{
  ESP_LOGD(TAG, "Client not alive, closing fd %d", fd);
  httpd_sess_trigger_close(wss_keep_alive_get_user_ctx(h), fd);
  return true;
}

///////////////////////////////////////////////////////////////////////////////
// check_client_alive_cb
//

bool
check_client_alive_cb(wss_keep_alive_t h, int fd)
{
  ESP_LOGD(TAG, "Checking if client (fd=%d) is alive", fd);
  struct async_resp_arg *resp_arg = malloc(sizeof(struct async_resp_arg));
  assert(resp_arg != NULL);
  resp_arg->hd = wss_keep_alive_get_user_ctx(h);
  resp_arg->fd = fd;

  if (httpd_queue_work(resp_arg->hd, send_ping, resp_arg) == ESP_OK) {
    return true;
  }
  free(resp_arg);
  return false;
}

///////////////////////////////////////////////////////////////////////////////
// start_wss_echo_server
//

// static httpd_handle_t
// start_wss_echo_server(void)
// {
//   // Prepare keep-alive engine
//   wss_keep_alive_config_t keep_alive_config = KEEP_ALIVE_CONFIG_DEFAULT();
//   keep_alive_config.max_clients             = max_clients;
//   keep_alive_config.client_not_alive_cb     = client_not_alive_cb;
//   keep_alive_config.check_client_alive_cb   = check_client_alive_cb;
//   wss_keep_alive_t keep_alive               = wss_keep_alive_start(&keep_alive_config);

//   // Start the httpd server
//   httpd_handle_t server = NULL;
//   ESP_LOGI(TAG, "Starting server");

//   httpd_config_t conf   = HTTPD_DEFAULT_CONFIG();
//   conf.max_open_sockets = max_clients;
//   conf.global_user_ctx  = keep_alive;
//   conf.open_fn          = wss_open_fd;
//   conf.close_fn         = wss_close_fd;

//   // extern const unsigned char servercert_start[] asm("_binary_servercert_pem_start");
//   // extern const unsigned char servercert_end[] asm("_binary_servercert_pem_end");
//   // conf.servercert     = servercert_start;
//   // conf.servercert_len = servercert_end - servercert_start;

//   // extern const unsigned char prvtkey_pem_start[] asm("_binary_prvtkey_pem_start");
//   // extern const unsigned char prvtkey_pem_end[] asm("_binary_prvtkey_pem_end");
//   // conf.prvtkey_pem = prvtkey_pem_start;
//   // conf.prvtkey_len = prvtkey_pem_end - prvtkey_pem_start;
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
